rkstlohchab/esp32-rkstlohchab/ESP32-DIV/shared.h

#ifndef SHARED_H
#define SHARED_H
#include <stdint.h>
#include "BoardConfig.h"
#include "NavInput.h"   /* PORT: NavExpander = PCF8574 or JoystickNav */

/*──────────────────── Colors ────────────────────*/
const uint16_t GRAY = 0x8410, BLUE = 0x001F, RED = 0xF800,
               GREEN  = 0xB721, BLACK = 0x0000, WHITE = 0xFFFF,
               LIGHT_GRAY = 0xC618, DARK_GRAY = 0x4208;

uint16_t uiUniversalColor();
#define ORANGE uiUniversalColor()
               
#define TFT_DARKBLUE   0x3166
#define TFT_LIGHTBLUE  0x051F
#define TFTWHITE       0xFFFF
#define TFT_GRAY       0x8410

#ifdef TFT_GREEN
#undef TFT_GREEN
#endif
#define TFT_GREEN GREEN
#ifdef TFT_GREENYELLOW
#undef TFT_GREENYELLOW
#endif
#define TFT_GREENYELLOW GREEN

#define BG_Dark        0x20e4
#define BG_Light       0xf7de
#define FG_Dark        0x3166
#define FG_Light       0xe73c
#define LINE_Dark      0x8410  
#define LINE_Light     0x8410  
#define ICON_Dark      0xFBE4 
#define ICON_Light     0xFBE4
#define TEXT_Dark      0xFFFF
#define TEXT_Light     0x0000   
#define UI_ACCENT      0x3166

#define L_Dark        0x4208
#define L_Light       0xC618

// Default background for feature screens (separate from main menu background).
// Currently black, but you can change this one define to restyle all features.
#ifndef FEATURE_BG
#define FEATURE_BG BLACK
#endif

#define SELECTED_ICON_COLOR UI_ICON

/*──────────────────── UI Defaults ────────────────────*/
#ifndef UI_BG
#define UI_BG UI.bg
#endif
#ifndef UI_FG
#define UI_FG UI.fg
#endif
#ifndef UI_ICON
#define UI_ICON UI.icon
#endif
#ifndef UI_TEXT
#define UI_TEXT UI.text
#endif
#ifndef UI_LINE
#define UI_LINE UI.line
#endif
#ifndef UI_LABLE
#define UI_LABLE UI.lable
#endif
#ifndef UI_ACCENT
#define UI_ACCENT UI.accent
#endif
#ifndef UI_WARN
#define UI_WARN UI.warn
#endif
#ifndef UI_OK
#define UI_OK GREEN
#endif

/*──────────────────── Project Info ────────────────────*/
#ifndef ESP32DIV_NAME
#define ESP32DIV_NAME "ESP32-DIV"
#endif
#ifndef ESP32DIV_VERSION
#define ESP32DIV_VERSION "v1.7.2"
#endif


#define DEVICE_OWNER_NAME "rkstlohchab"

/*──────────────────── Board Selection ────────────────────*/
// Default is selected in BoardConfig.h. You can also pass a BOARD_* define
// from your build flags to target a board without editing source.
#if !defined(BOARD_ESP32_DIV_V2) && !defined(BOARD_CYD) && !defined(BOARD_ESP32_DIV_V1)
#define BOARD_ESP32_DIV_V2
#endif

#if (defined(BOARD_ESP32_DIV_V2) + defined(BOARD_CYD) + defined(BOARD_ESP32_DIV_V1)) > 1
#error "Select only one board: BOARD_ESP32_DIV_V2, BOARD_ESP32_DIV_V1, or BOARD_CYD"
#endif
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
